danielss24/TFG_EPS_DSS/Memoria/Latex/varios/estudioDron.tex

Se han realizado numerosas configuraciones para estabilizar tiempo de vuelo y carga máxima del dron, obteniendo el mejor resultado en la imagen de a continuación \ref{FIG:estudioDron}.
\begin{figure}[Estudio técnico de dron]{FIG:estudioDron}{En esta imagen se muestran los datos obtenidos mediante una herramienta de internet, eCalc \cite{DroneConfig}, para el estudio de componentes para dron.}
	\image{1\textwidth}{}{estudioDron}
\end{figure}
