danielss24/TFG_EPS_DSS/Memoria/Latex/inicio/agradecimientos.tex

En primer lugar me gustaría agradecer el esfuerzo y empeño que han demostrado todas las personas del departamento donde he hecho este TFG, empezando por mi tutor Stefan Palzer, por guiarme y ayudarme a realizar este trabajo, a Álvaro Ortiz por sus consejos de recién doctorado y su ingenio que ha arreglado algún que otro problemilla y, sobre todo, a Patricia González, mi compañera de ideas y sufrimiento durante todo este proceso de investigación y desarrollo de nuestro trabajo de final de grado. 

Por otro lado quiero agradecer el apoyo que he recibido de mi familia ya que, sin ellos no podría haber finalizado esta etapa de mi vida plasmada en este último proyecto de la carrera que he llevado a cabo.

En último lugar pero no menos importante quiero agradecer a mis amigos y compañeros a los que han terminado o aún siguen en la carrera, especial mención a la promoción de este año con los que he compartido tanto risas como lágrimas. 

Muchas gracias a todos.
