danielss24/TFG_EPS_DSS/Memoria/Latex/varios/codigoPlotWind0.tex

\PythonCode[COD:CODIGOPLOTSCATTER]{Código de scatterFit}{Código de gráfica para imagen \ref{FIG:scatterFit}}{plotWind.py}{245}{281}{1}
