danielss24/TFG_EPS_DSS/Memoria/Latex/varios/codigoPlotWind1.tex

\PythonCode[COD:CODIGOHEATMAP]{Código de mapa de calor - parte 1}{Código de gráfica para imagen \ref{FIG:MAPACALOR}(a)}{plotWind.py}{283}{320}{1}

\PythonCode[COD:CODIGOHEATMAP2]{Código de mapa de calor - parte 2}{Código de gráfica para imagen \ref{FIG:MAPACALOR}(a)}{plotWind.py}{321}{328}{39}
