danielss24/TFG_EPS_DSS/Memoria/Latex/varios/codigoPlotWind2.tex

Para la ilustración de un mapa 2D con 4 vectores se ha tenido que realizar una conversión de un conjunto de puntos en un vector con dos direcciones.

\PythonCode[COD:CODIGOGRAFICA2D]{Código de gráfica 2D - parte 1}{Código de gráfica para imagen \ref{FIG:PLANOSMEDIDAS}(a) y \ref{FIG:PLANOSMEDIDAS}(b)}{plotWind.py}{330}{360}{1}

\PythonCode[COD:CODIGOGRAFICA2D2]{Código de gráfica 2D - parte 2}{Código de gráfica para imagen \ref{FIG:PLANOSMEDIDAS}(a) y \ref{FIG:PLANOSMEDIDAS}(b)}{plotWind.py}{361}{381}{61}
