danielss24/TFG_EPS_DSS/Memoria/Latex/varios/codigoPlotWind3.tex

La ilustración de los datos en 3D ha tenido que llevar a cabo una conversión de un conjunto de puntos variables en un vector, conformando de esta forma un mapa 3D de 8 vectores.

\PythonCode[COD:CODIGOGRAFICA3D]{Código de gráfica 3D - parte 1}{Código de gráfica para imagen \ref{FIG:mapa3d}}{plotWind.py}{383}{410}{1}

\PythonCode[COD:CODIGOGRAFICA3DPart2]{Código de gráfica 3D - parte 2}{Código de gráfica para imagen \ref{FIG:mapa3d}}{plotWind.py}{411}{461}{29}

\PythonCode[COD:CODIGOGRAFICA3DPart3]{Código de gráfica 3D - parte 3}{Código de gráfica para imagen \ref{FIG:mapa3d}}{plotWind.py}{462}{484}{79}
