danielss24/TFG_EPS_DSS/Documentacion/Dron/Old/HobbyKing ™ TORTAZO 300.docx

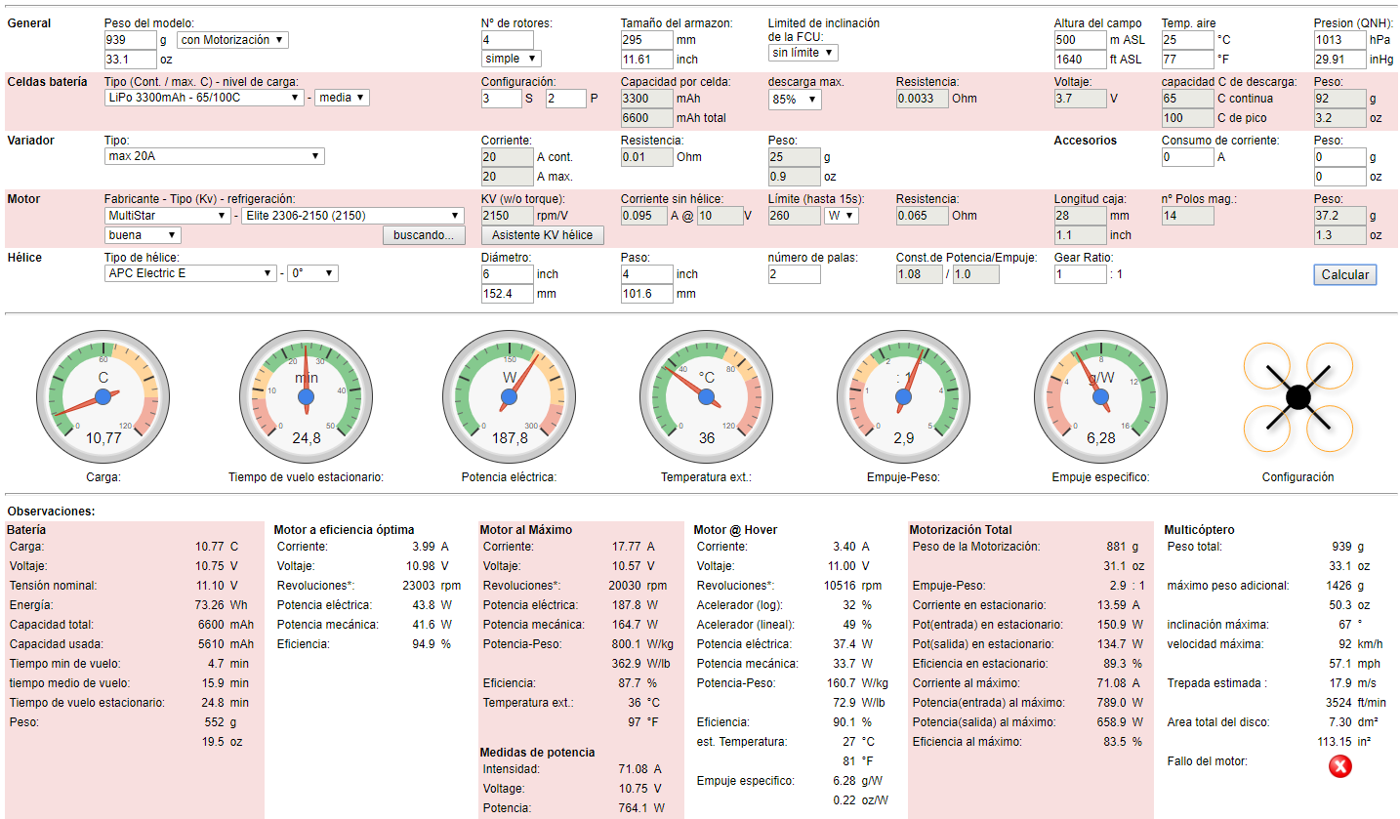
[picture p22: figure]
