danielss24/TFG_EPS_DSS/Memoria/Latex/img/3axisforces.png

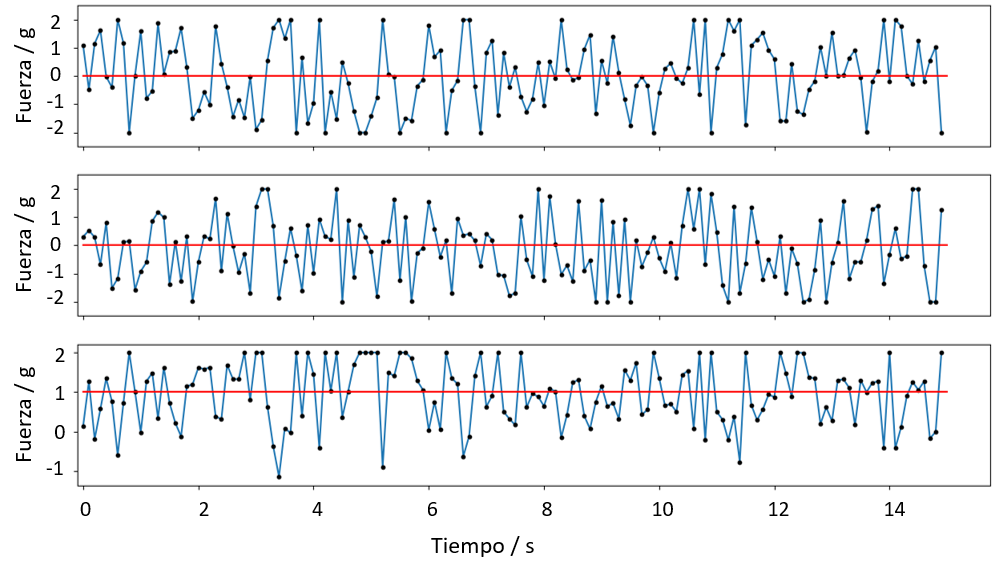
Memoria/Latex/img/3axisforces.png
