danielss24/TFG_EPS_DSS/Memoria/Latex/img/acoplamientosDron.png

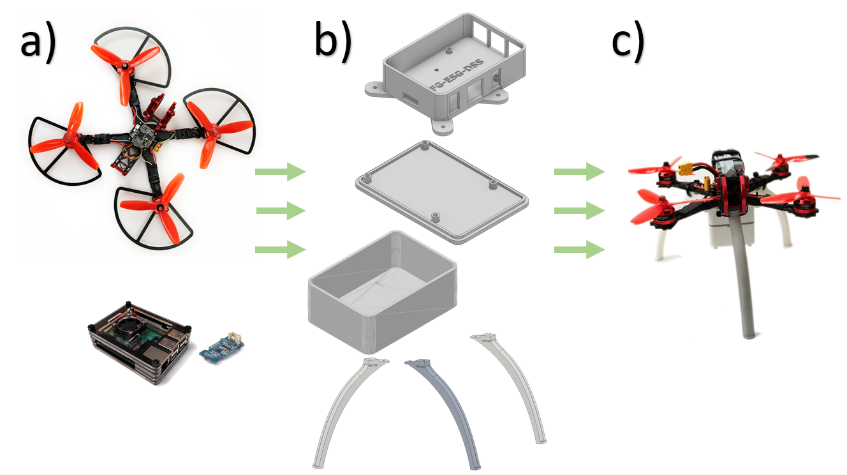
Memoria/Latex/img/acoplamientosDron.png
