danielss24/TFG_EPS_DSS/Memoria/Latex/img/bateriaDron.PNG

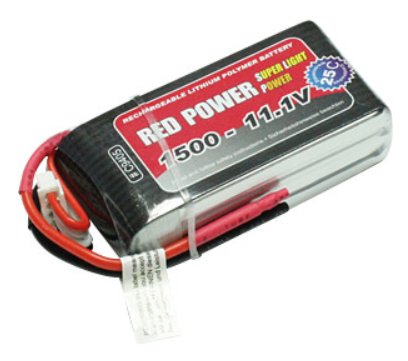
Memoria/Latex/img/bateriaDron.PNG
