danielss24/TFG_EPS_DSS/Memoria/Latex/img/chasis2Dron.PNG

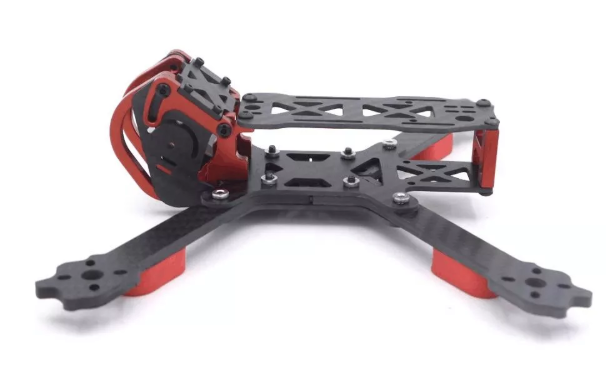
Memoria/Latex/img/chasis2Dron.PNG
