danielss24/TFG_EPS_DSS/Memoria/Latex/img/chasisDron.PNG

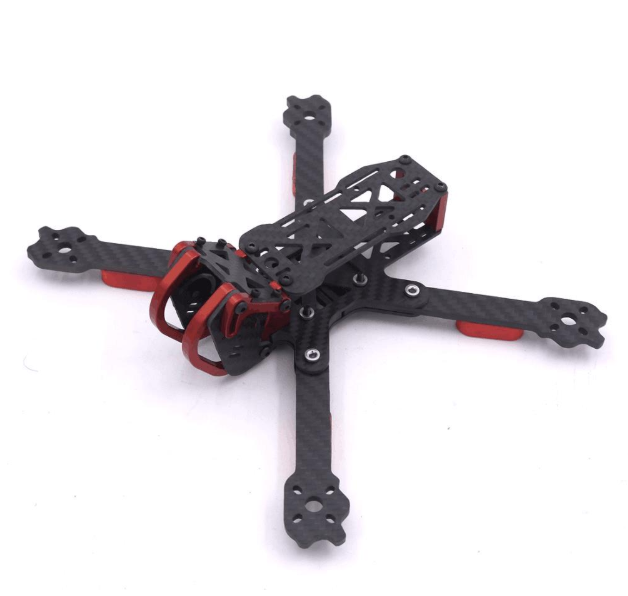
Memoria/Latex/img/chasisDron.PNG
