danielss24/TFG_EPS_DSS/Memoria/Latex/img/ChasisRaspberryDron.PNG

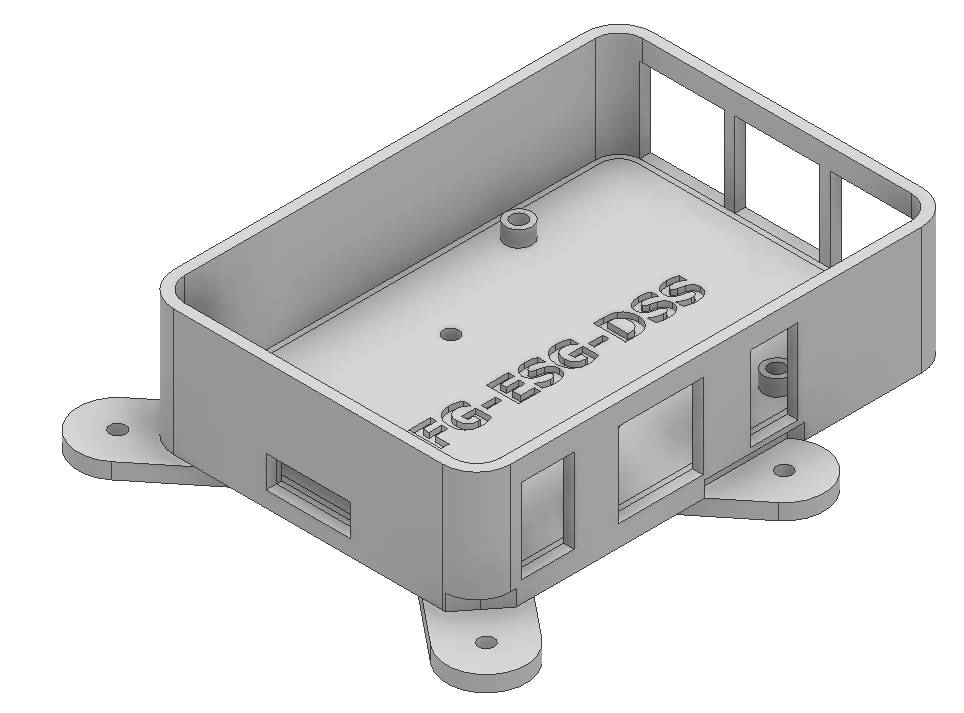
Memoria/Latex/img/ChasisRaspberryDron.PNG
