danielss24/TFG_EPS_DSS/Memoria/Latex/img/controladoraDron.PNG

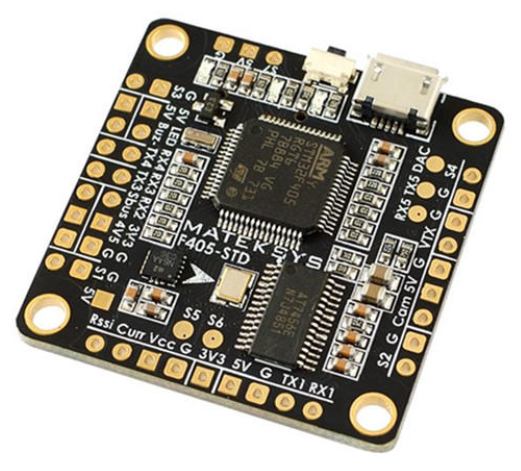
Memoria/Latex/img/controladoraDron.PNG
