danielss24/TFG_EPS_DSS/Memoria/Latex/img/diagramaPlacaControladora2.png

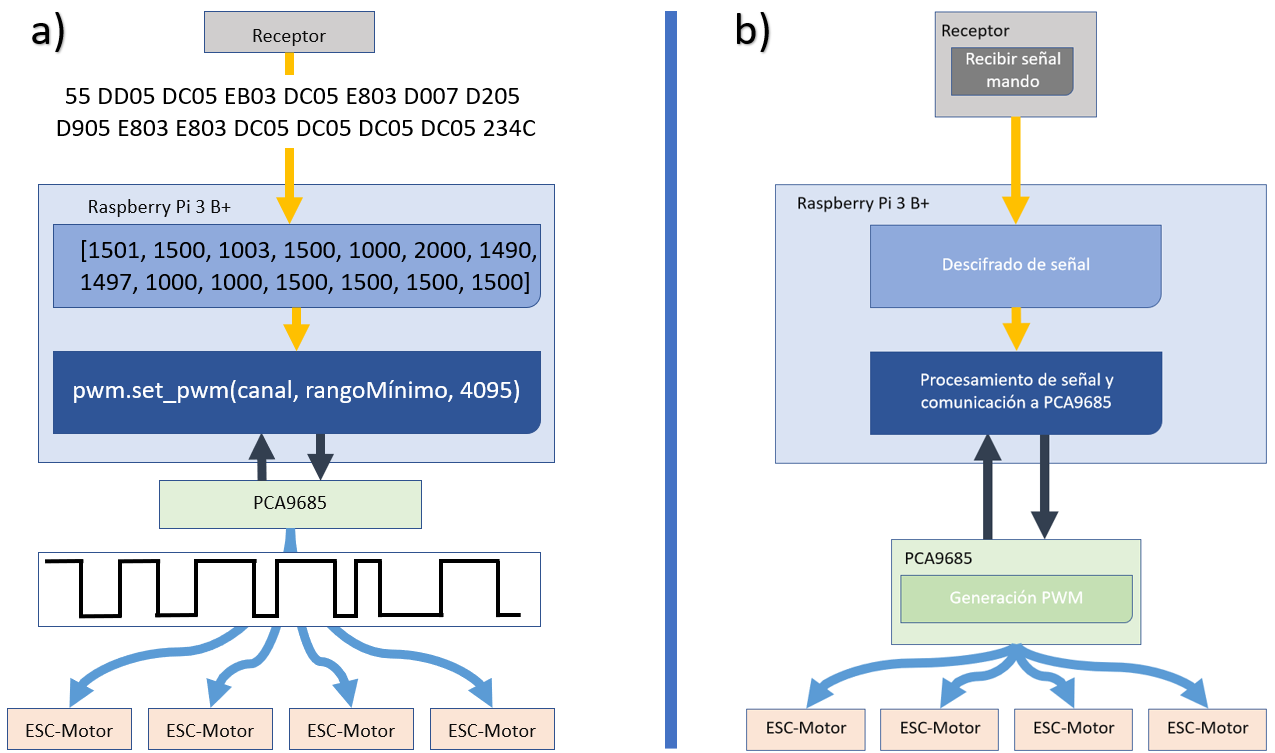
Memoria/Latex/img/diagramaPlacaControladora2.png
