danielss24/TFG_EPS_DSS/Memoria/Latex/img/diagramaPlacaControladora.png

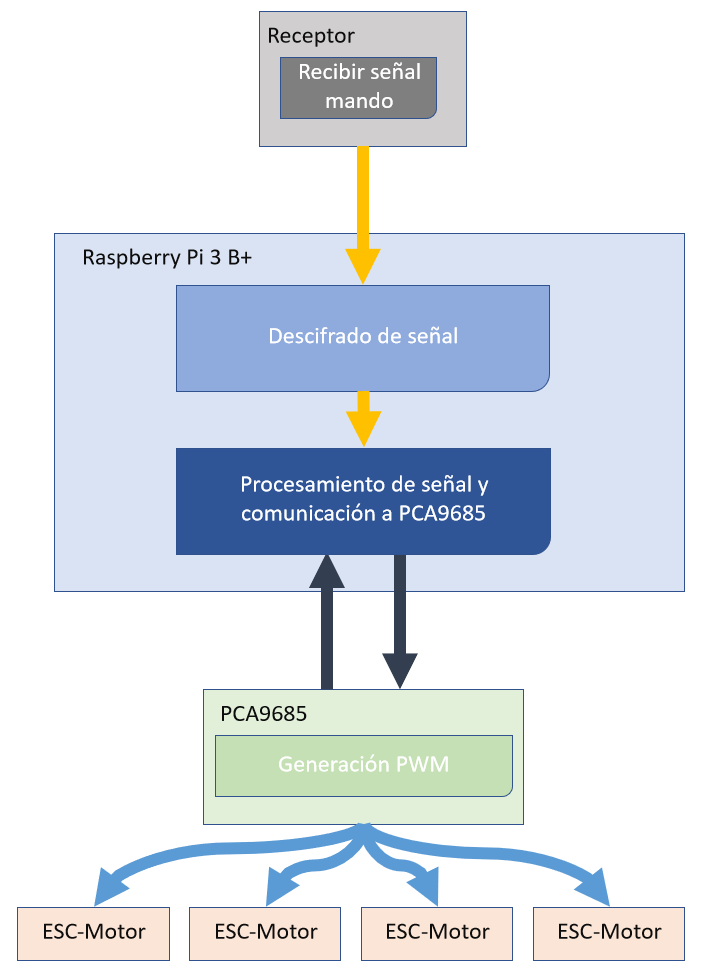
Memoria/Latex/img/diagramaPlacaControladora.png
