danielss24/TFG_EPS_DSS/Memoria/Latex/img/dronCompleto2.jpg

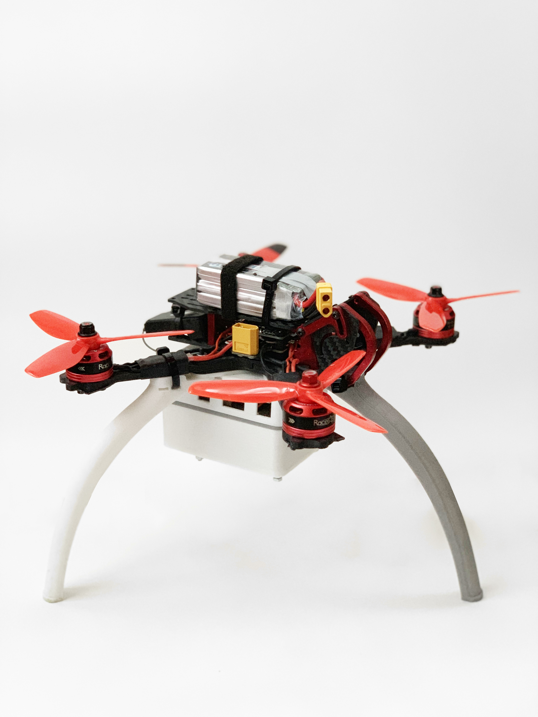
Memoria/Latex/img/dronCompleto2.jpg
