danielss24/TFG_EPS_DSS/Memoria/Latex/img/dronCompleto.jpg

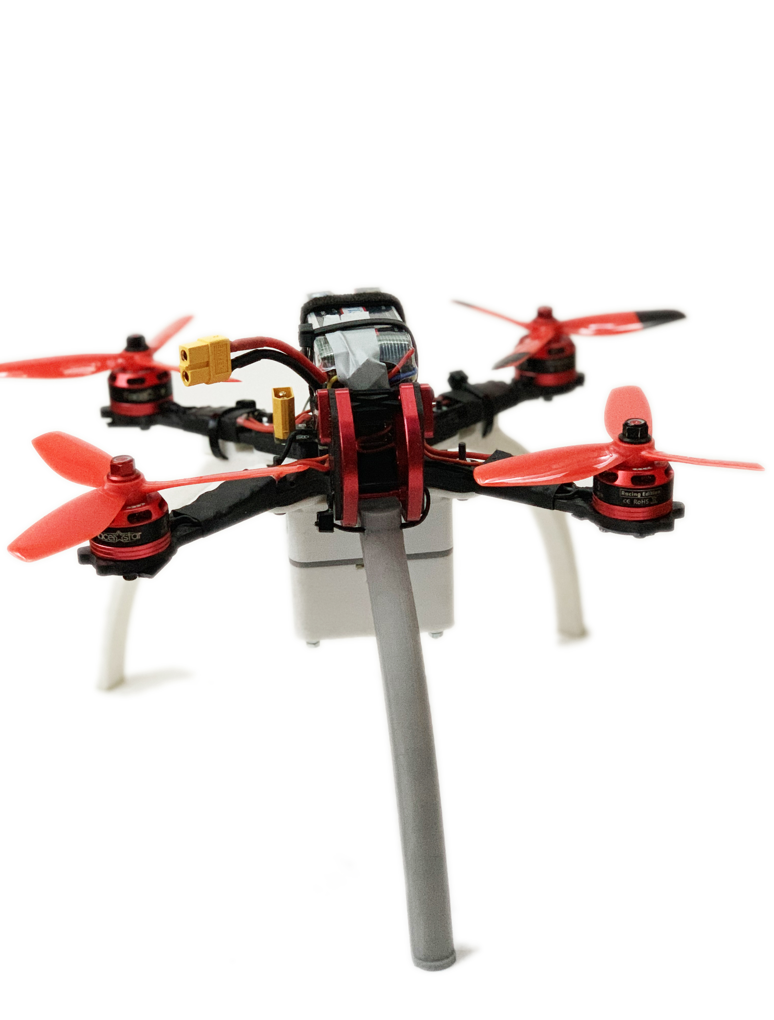
Memoria/Latex/img/dronCompleto.jpg
