danielss24/TFG_EPS_DSS/Memoria/Latex/img/dronVirgen2.jpg

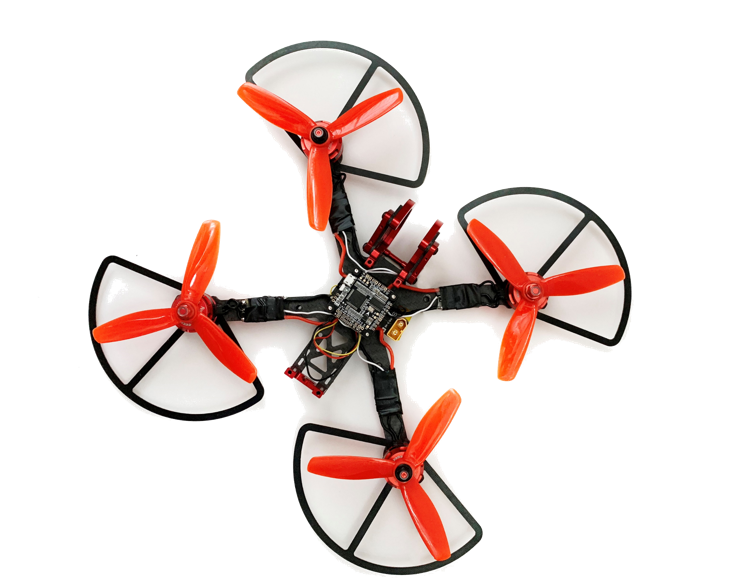
Memoria/Latex/img/dronVirgen2.jpg
