danielss24/TFG_EPS_DSS/Memoria/Latex/img/dronVirgen.jpg

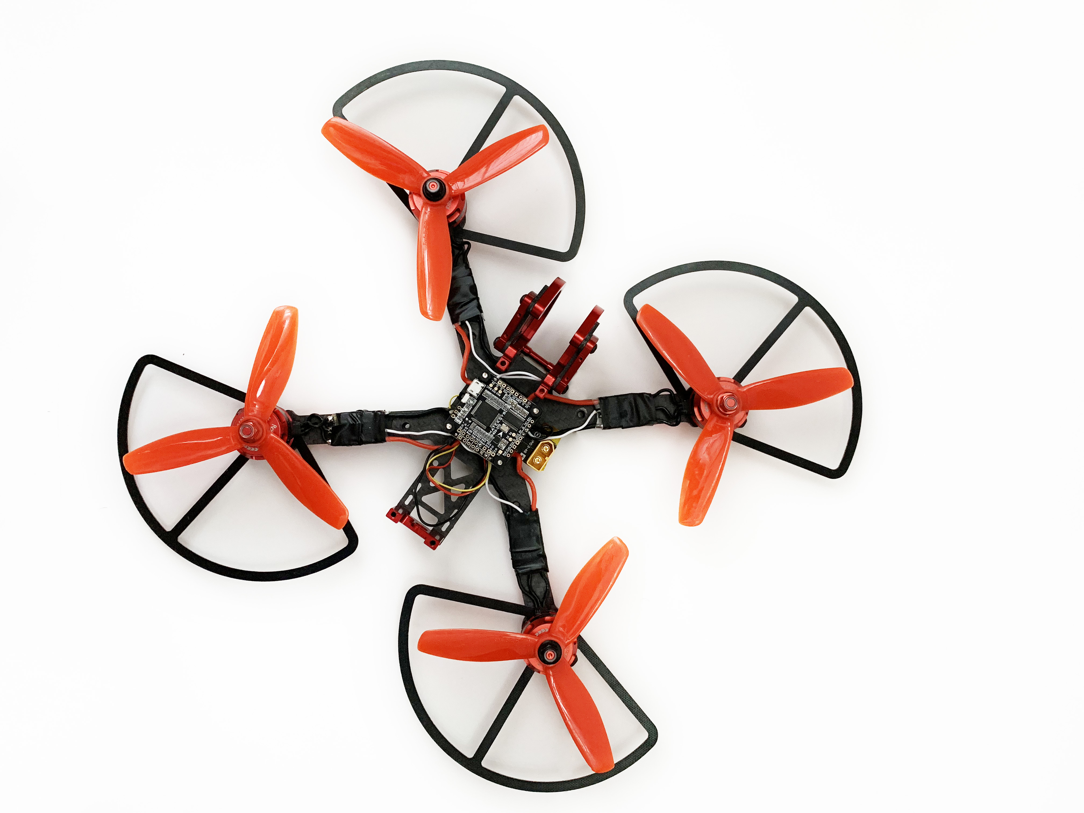
Memoria/Latex/img/dronVirgen.jpg
