danielss24/TFG_EPS_DSS/Memoria/Latex/img/dronVirgenPartes2.png

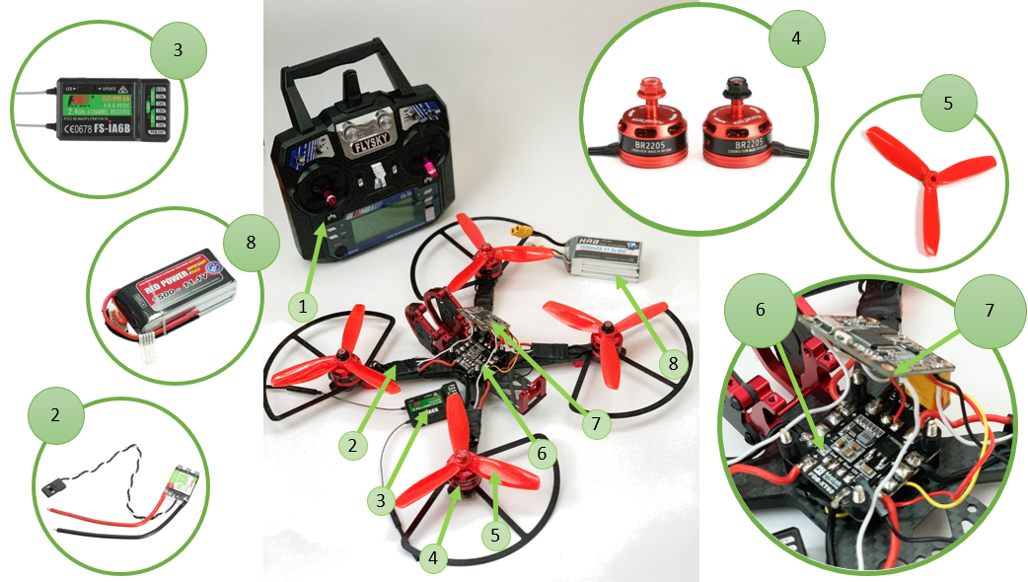
Memoria/Latex/img/dronVirgenPartes2.png
