danielss24/TFG_EPS_DSS/Memoria/Latex/img/dronVirgenPartes3.png

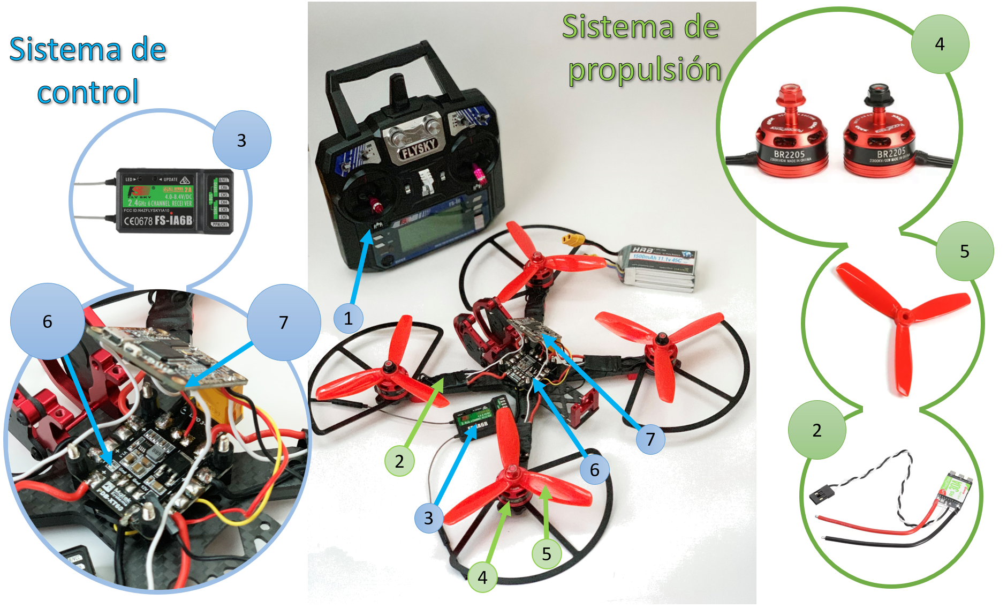
Memoria/Latex/img/dronVirgenPartes3.png
