danielss24/TFG_EPS_DSS/Memoria/Latex/img/dronVirgenPartes.png

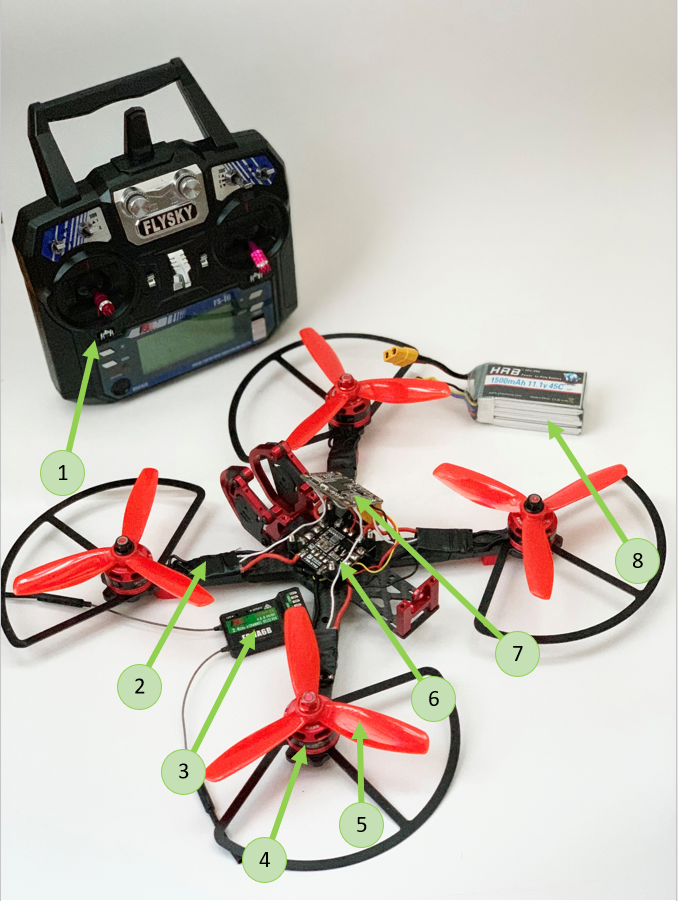
Memoria/Latex/img/dronVirgenPartes.png
