danielss24/TFG_EPS_DSS/Memoria/Latex/img/escDron.PNG

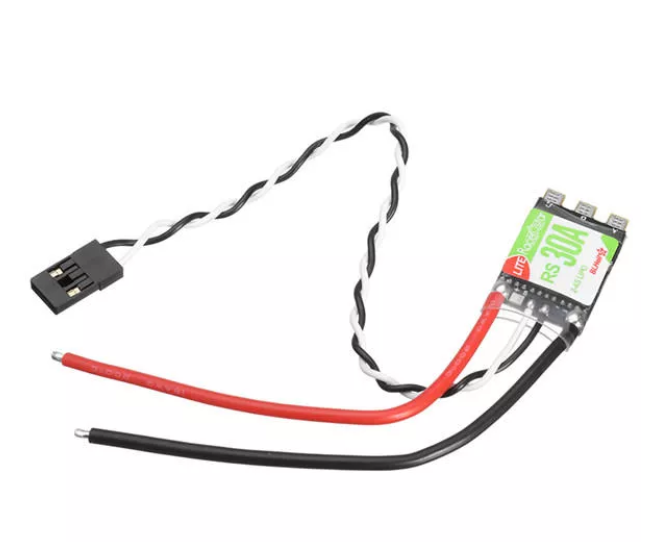
Memoria/Latex/img/escDron.PNG
