danielss24/TFG_EPS_DSS/Memoria/Latex/img/estructuraPrograma.png

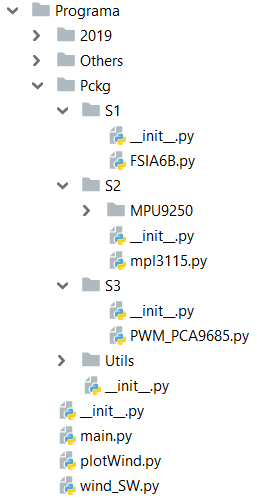
Memoria/Latex/img/estructuraPrograma.png
