danielss24/TFG_EPS_DSS/Memoria/Latex/img/gimansio0.jpg

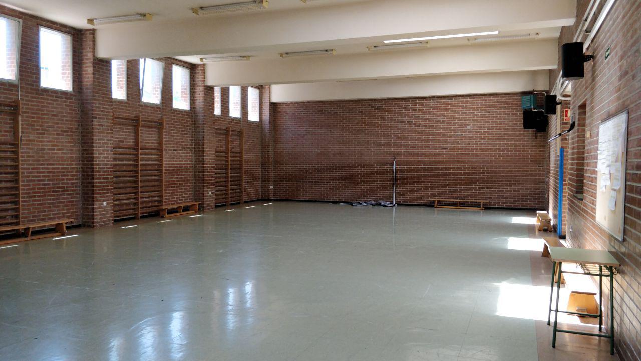
Memoria/Latex/img/gimansio0.jpg
