danielss24/TFG_EPS_DSS/Memoria/Latex/img/gimansio1.jpg

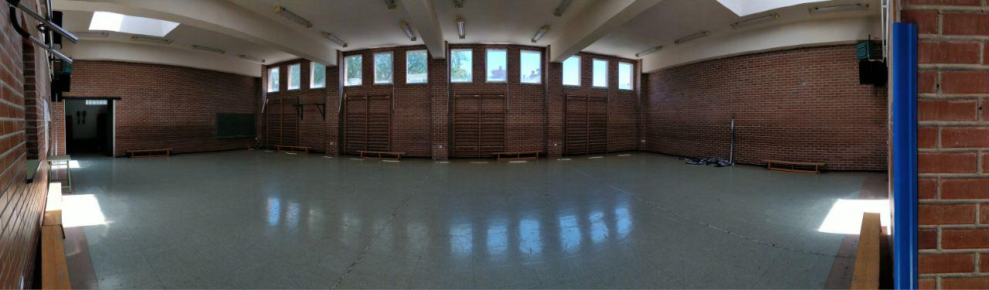
Memoria/Latex/img/gimansio1.jpg
