danielss24/TFG_EPS_DSS/Memoria/Latex/img/gimnasioPanoramicaPtsToma.png

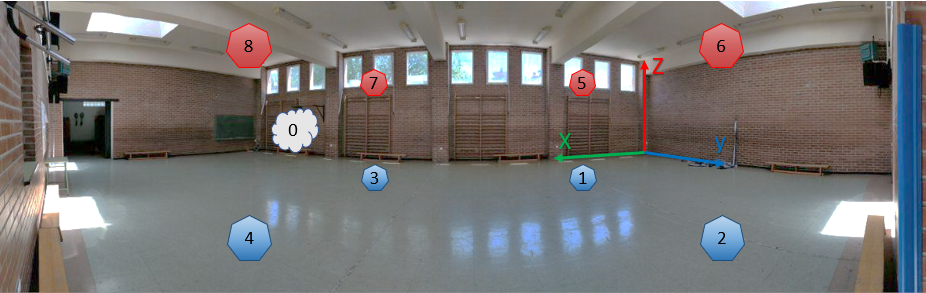
Memoria/Latex/img/gimnasioPanoramicaPtsToma.png
