danielss24/TFG_EPS_DSS/Memoria/Latex/img/gimnasioPanorámicaPtsToma.PNG

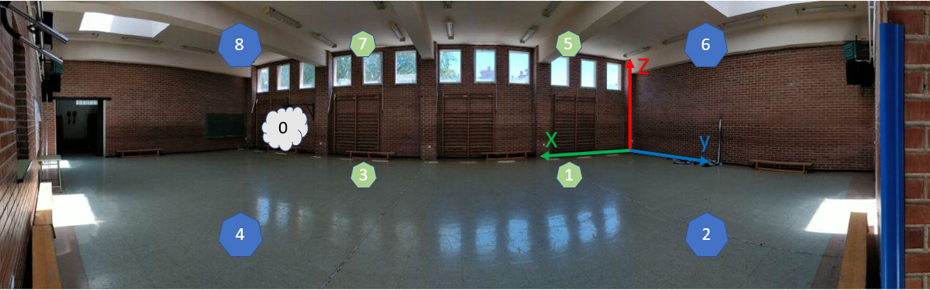
Memoria/Latex/img/gimnasioPanorámicaPtsToma.PNG
