danielss24/TFG_EPS_DSS/Memoria/Latex/img/graficasMapaCalor.png

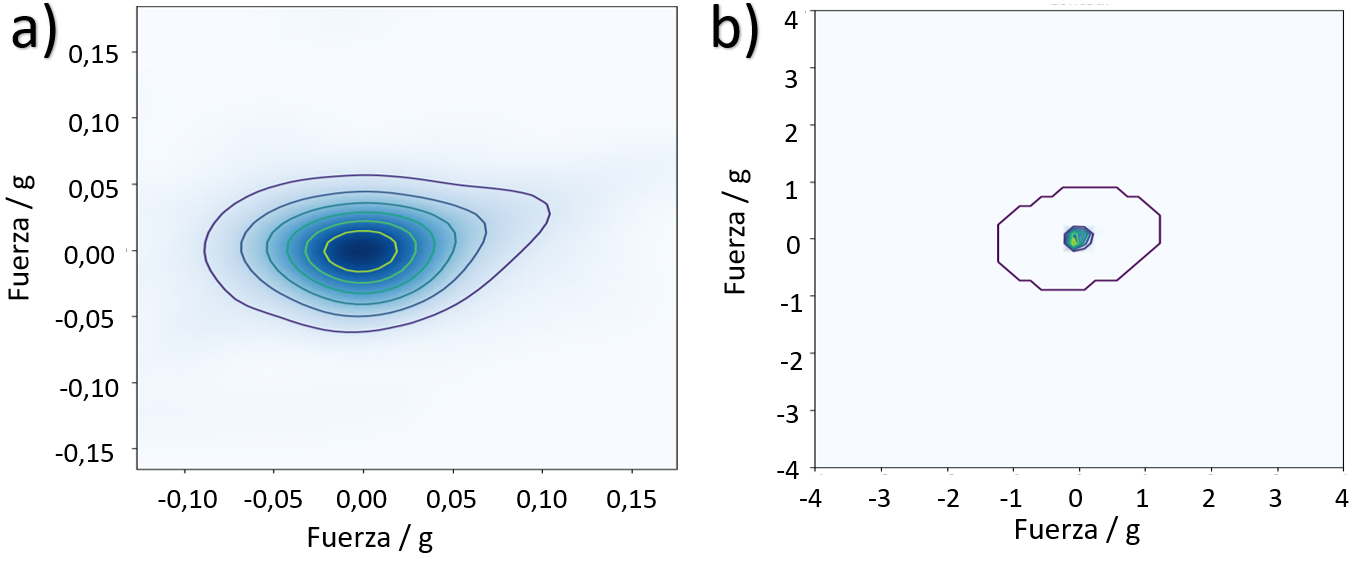
Memoria/Latex/img/graficasMapaCalor.png
