danielss24/TFG_EPS_DSS/Memoria/Latex/img/graficasplanoz0z1.png

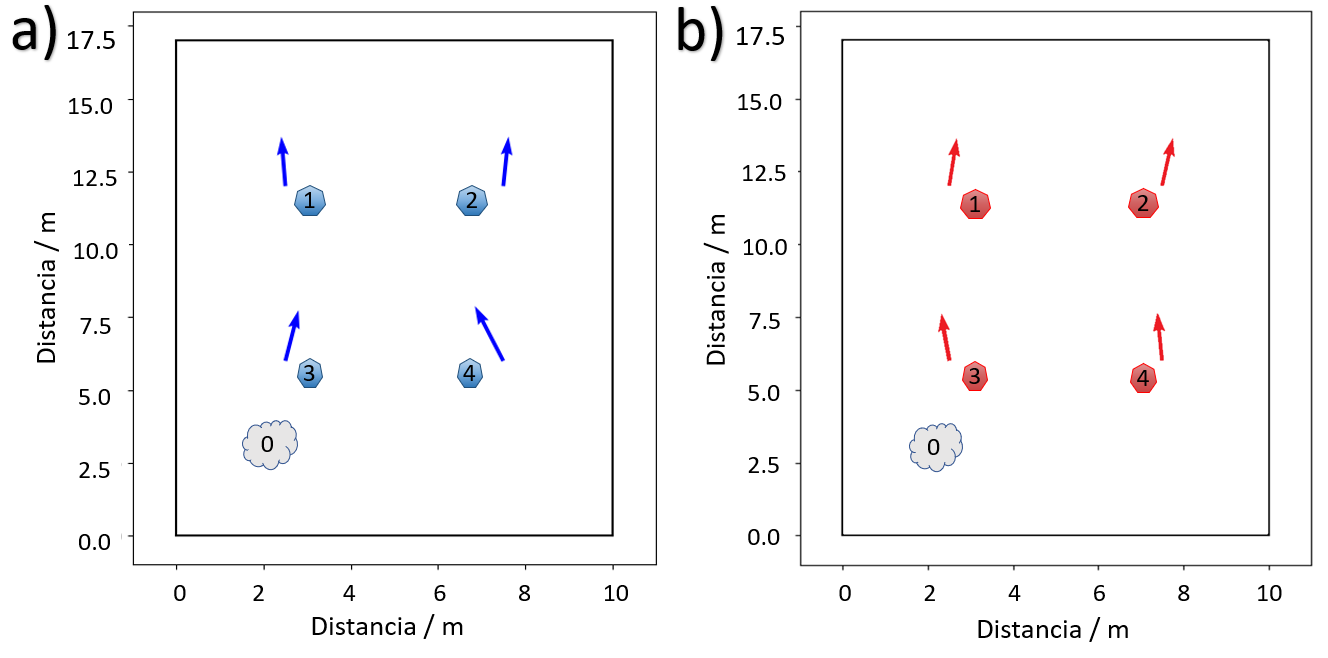
Memoria/Latex/img/graficasplanoz0z1.png
