danielss24/TFG_EPS_DSS/Memoria/Latex/img/heliceBullnose.PNG

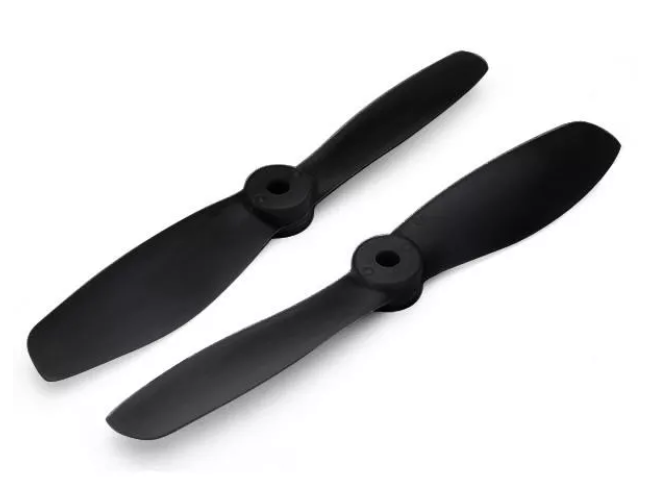
Memoria/Latex/img/heliceBullnose.PNG
