danielss24/TFG_EPS_DSS/Memoria/Latex/img/heliceHBullnose.jpg

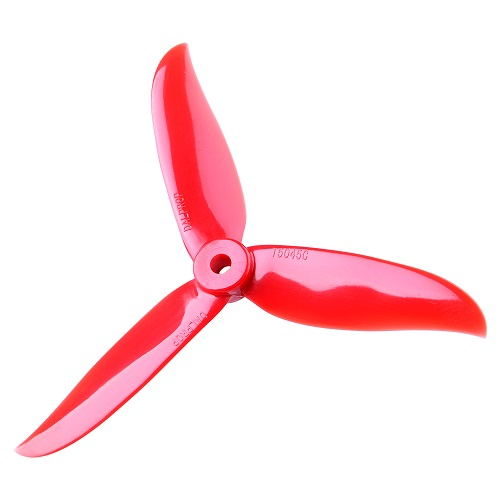
Memoria/Latex/img/heliceHBullnose.jpg
