danielss24/TFG_EPS_DSS/Memoria/Latex/img/helicePunta.jpg

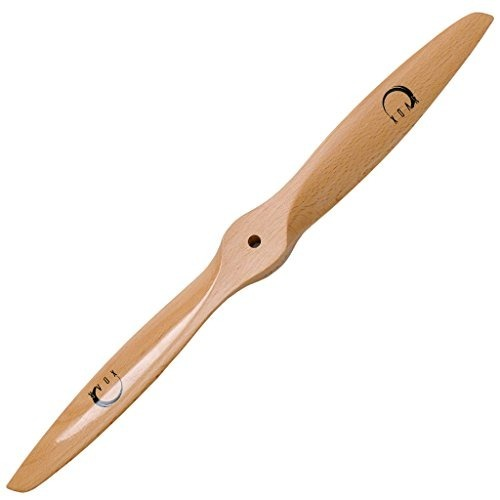
Memoria/Latex/img/helicePunta.jpg
