danielss24/TFG_EPS_DSS/Memoria/Latex/img/helicesDron.PNG

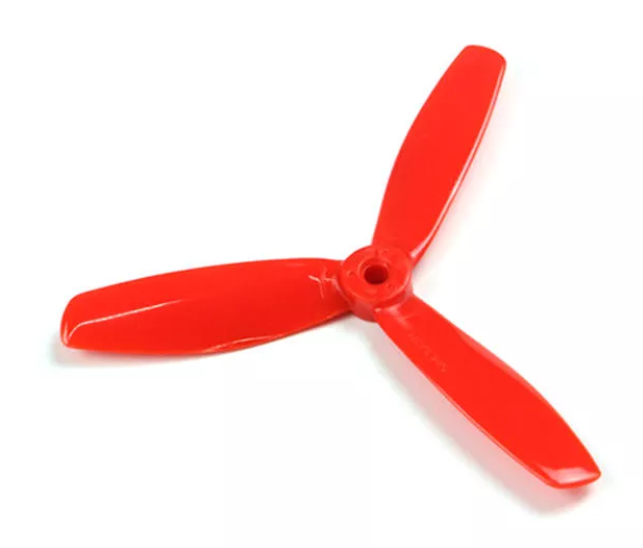
Memoria/Latex/img/helicesDron.PNG
