danielss24/TFG_EPS_DSS/Memoria/Latex/img/IMUAXES.png

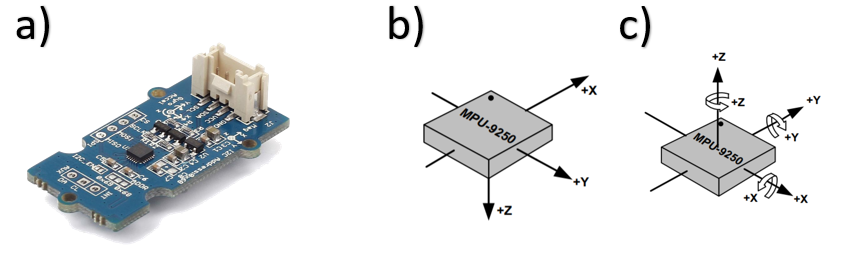
Memoria/Latex/img/IMUAXES.png
