danielss24/TFG_EPS_DSS/Memoria/Latex/img/introImg.png

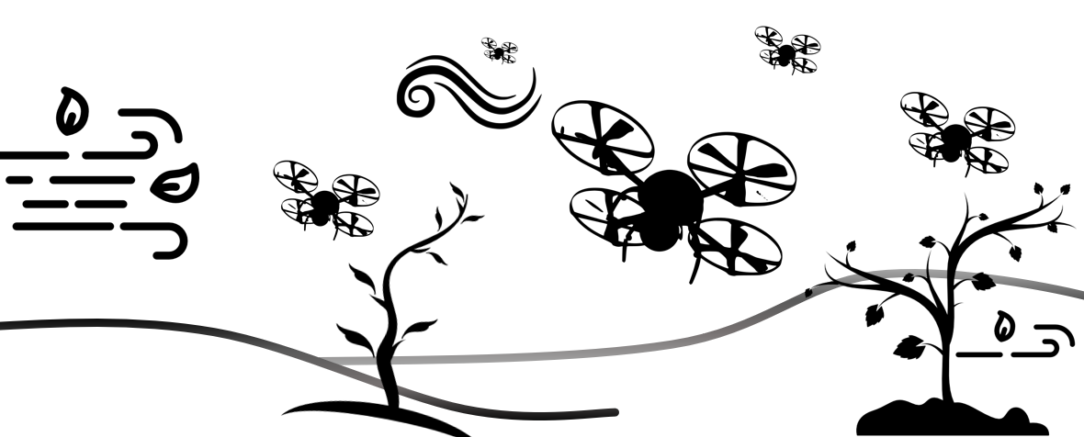
Memoria/Latex/img/introImg.png
