danielss24/TFG_EPS_DSS/Memoria/Latex/img/mandoDron.PNG

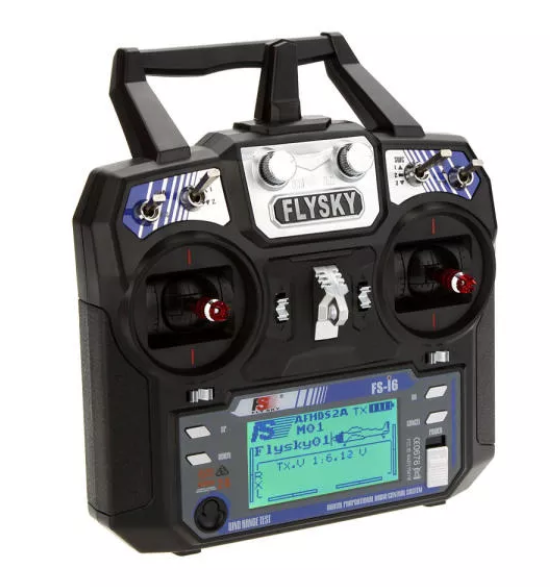
Memoria/Latex/img/mandoDron.PNG
