danielss24/TFG_EPS_DSS/Memoria/Latex/img/mapa3d.png

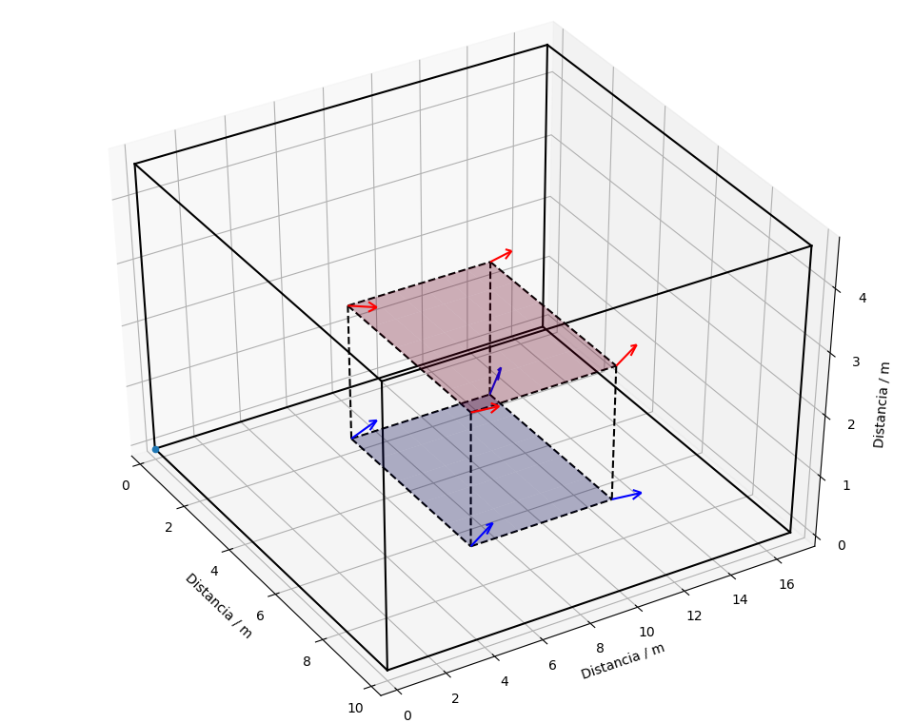
Memoria/Latex/img/mapa3d.png
