danielss24/TFG_EPS_DSS/Memoria/Latex/img/mapaCalor2.png

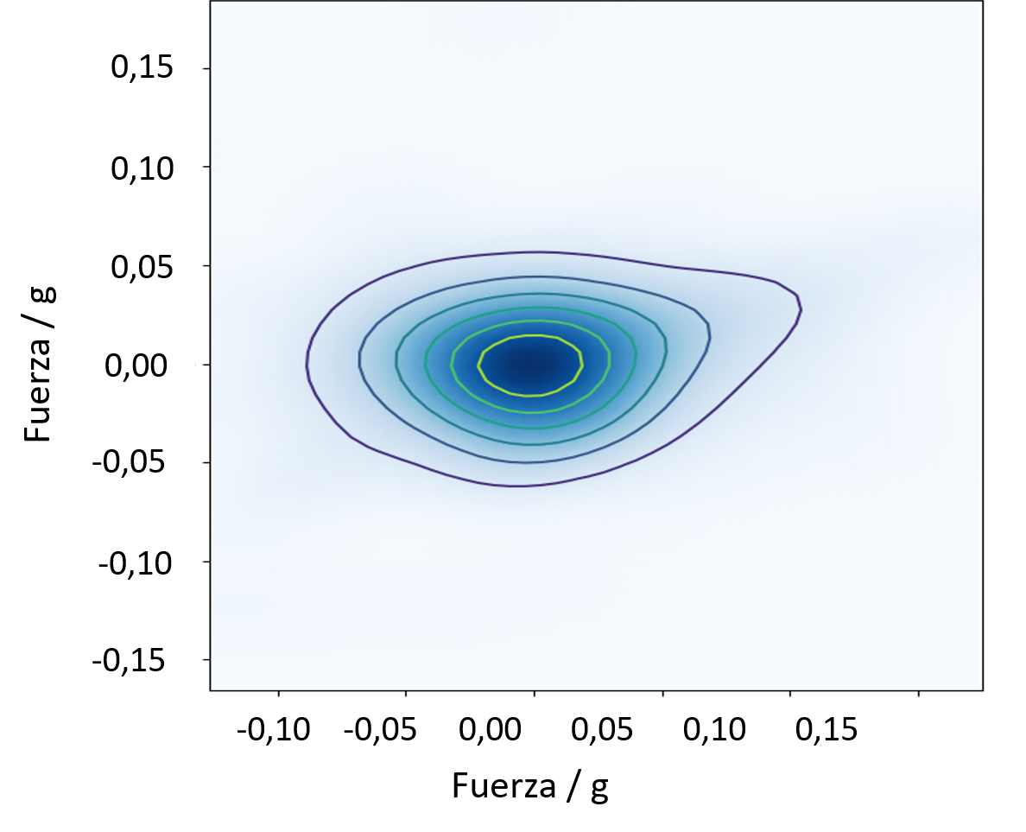
Memoria/Latex/img/mapaCalor2.png
