danielss24/TFG_EPS_DSS/Memoria/Latex/img/mapaCalor.png

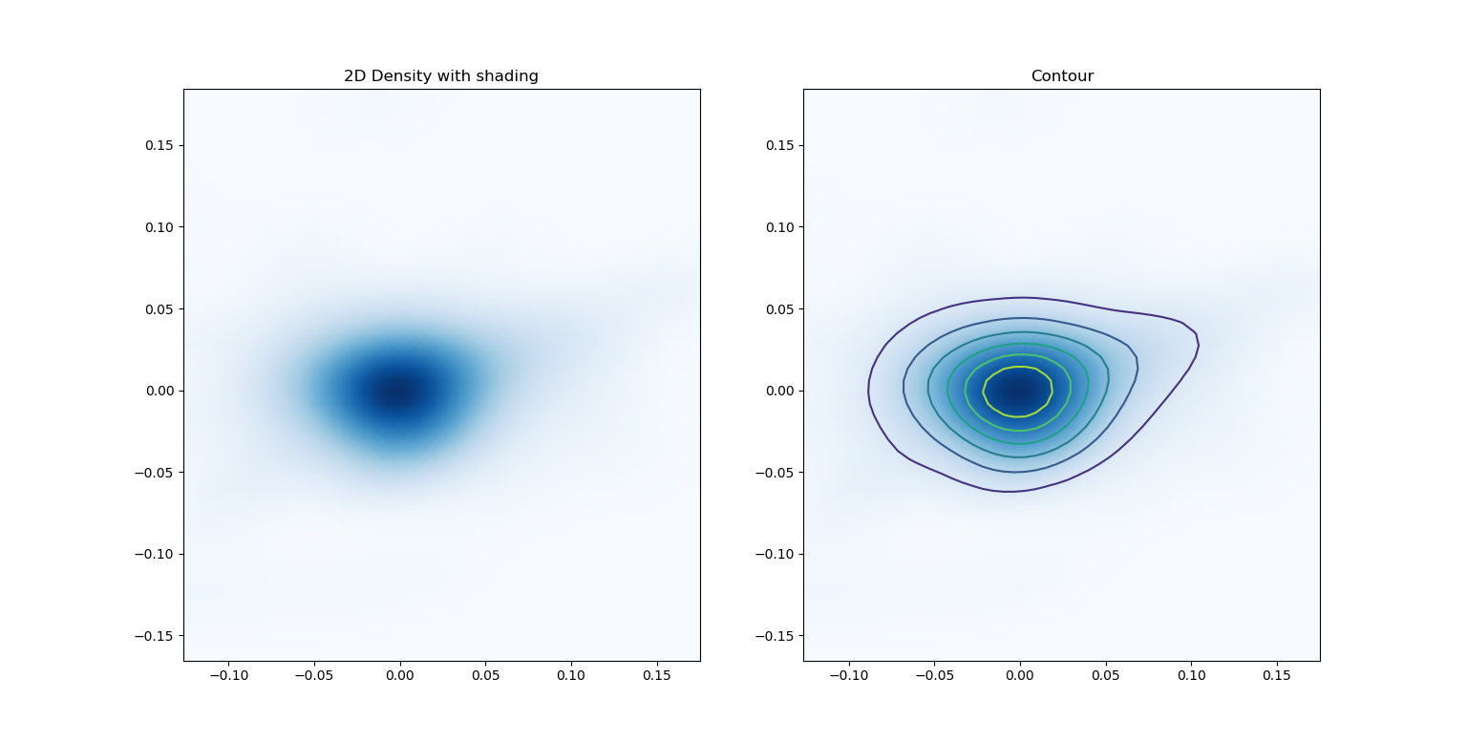
Memoria/Latex/img/mapaCalor.png
