danielss24/TFG_EPS_DSS/Memoria/Latex/img/mapaCalorSZ2.png

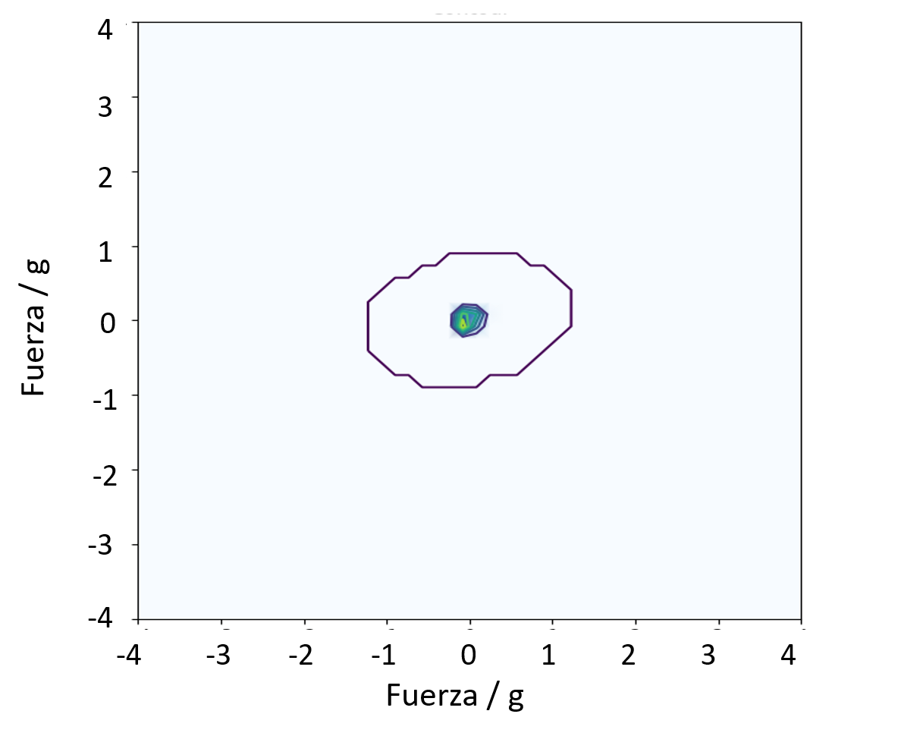
Memoria/Latex/img/mapaCalorSZ2.png
