danielss24/TFG_EPS_DSS/Memoria/Latex/img/mapaCalorSZ.png

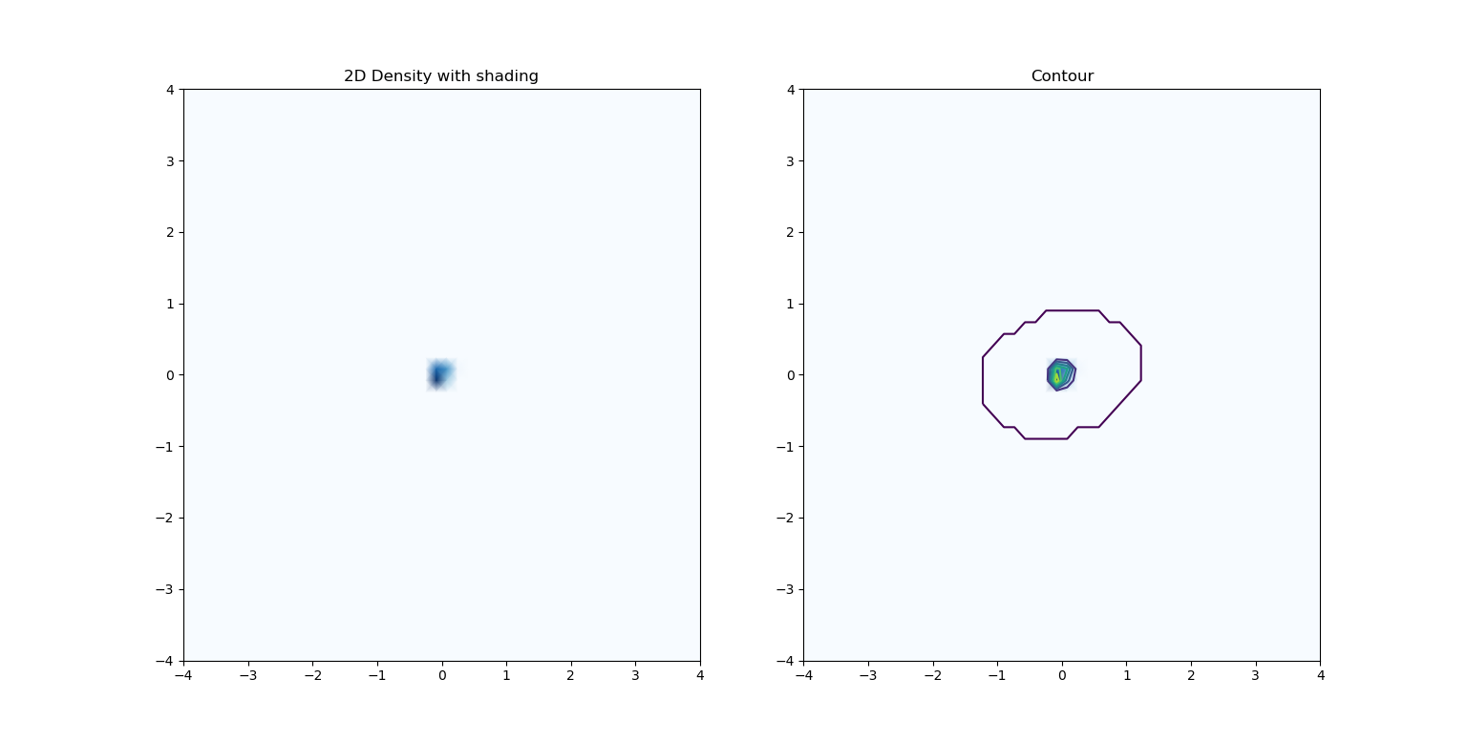
Memoria/Latex/img/mapaCalorSZ.png
