danielss24/TFG_EPS_DSS/Memoria/Latex/img/motoresDron.PNG

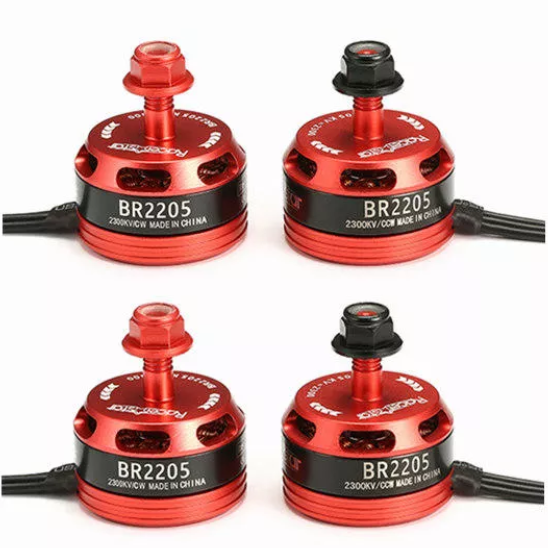
Memoria/Latex/img/motoresDron.PNG
