danielss24/TFG_EPS_DSS/Memoria/Latex/img/mpu9250AXES.png

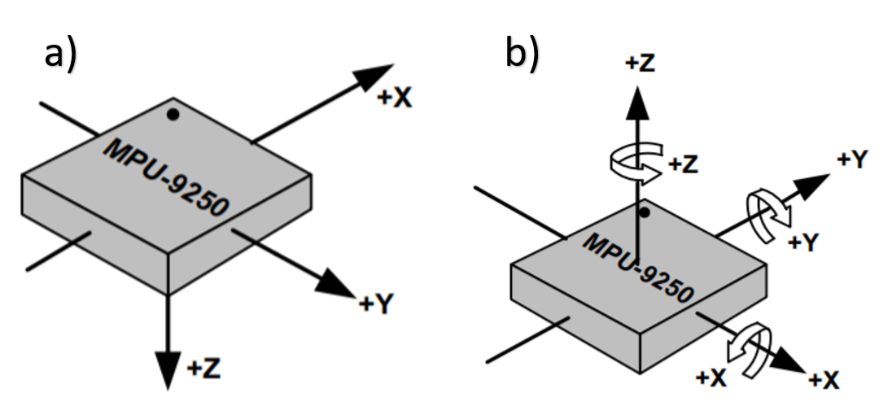
Memoria/Latex/img/mpu9250AXES.png
