danielss24/TFG_EPS_DSS/Memoria/Latex/img/PataDron.PNG

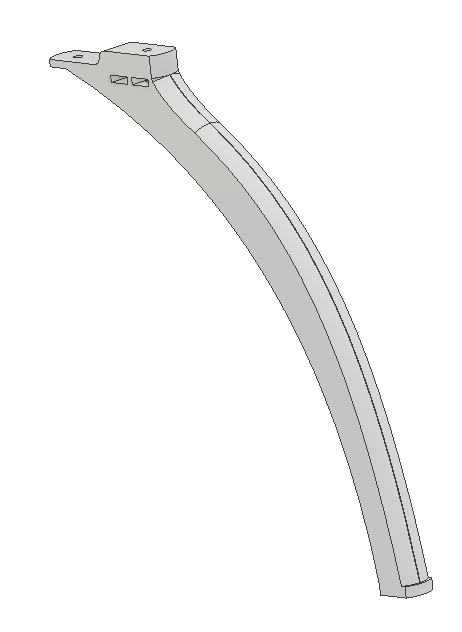
Memoria/Latex/img/PataDron.PNG
