danielss24/TFG_EPS_DSS/Memoria/Latex/img/pdbDron.PNG

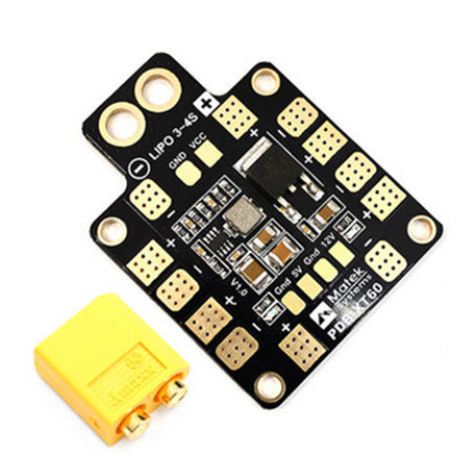
Memoria/Latex/img/pdbDron.PNG
