danielss24/TFG_EPS_DSS/Memoria/Latex/img/planoGimnasio.png

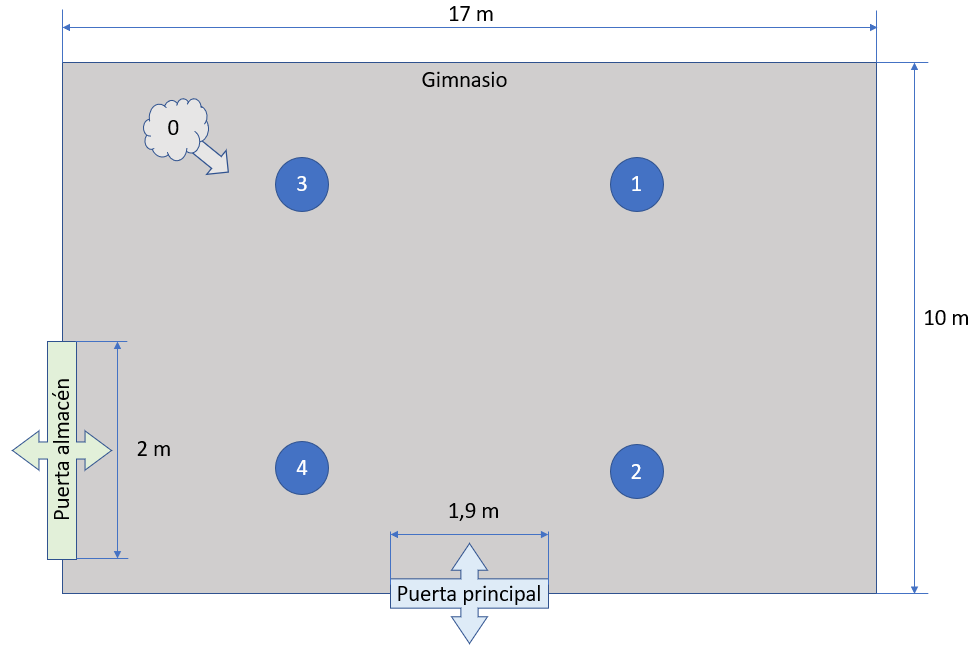
Memoria/Latex/img/planoGimnasio.png
