danielss24/TFG_EPS_DSS/Memoria/Latex/img/Plots/3axisforces.png

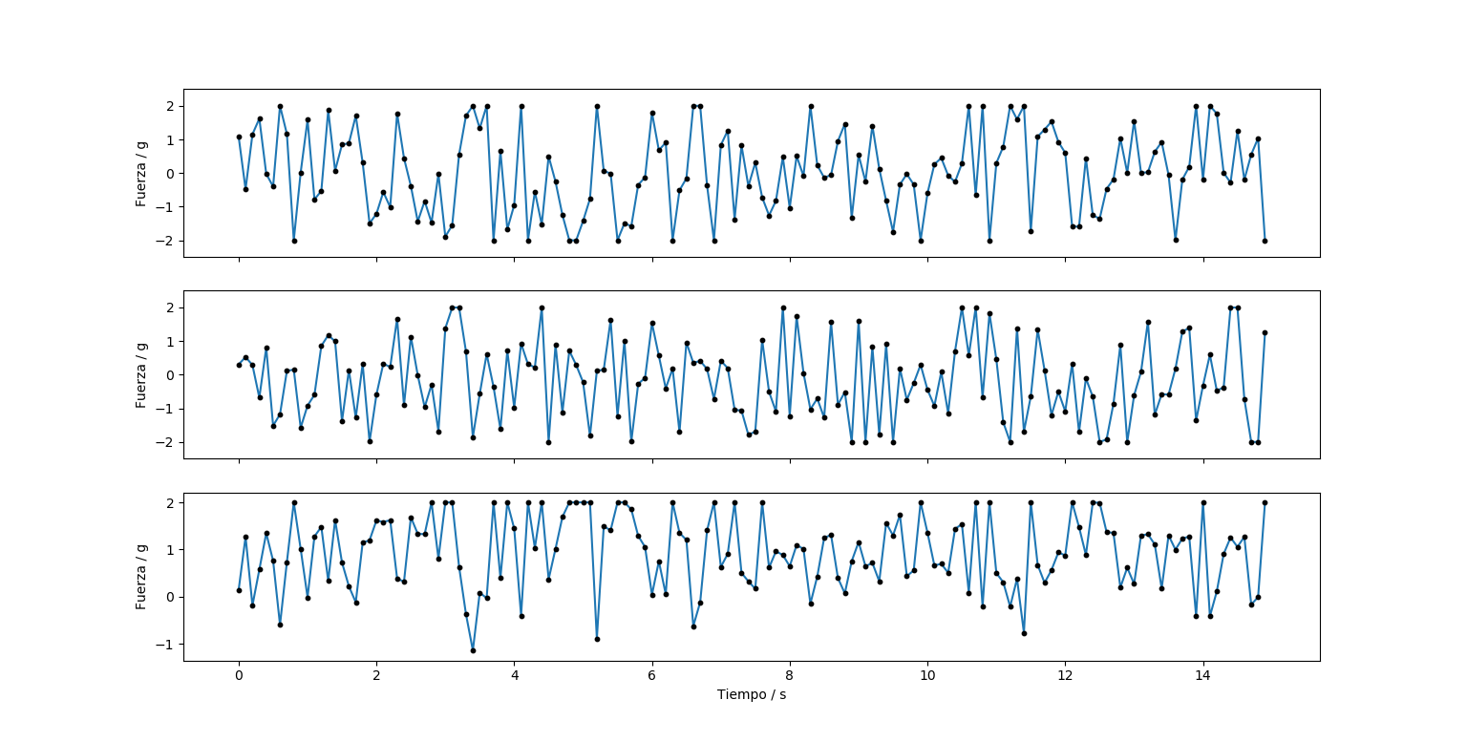
Memoria/Latex/img/Plots/3axisforces.png
