danielss24/TFG_EPS_DSS/Memoria/Latex/img/Plots/scatterFit.png

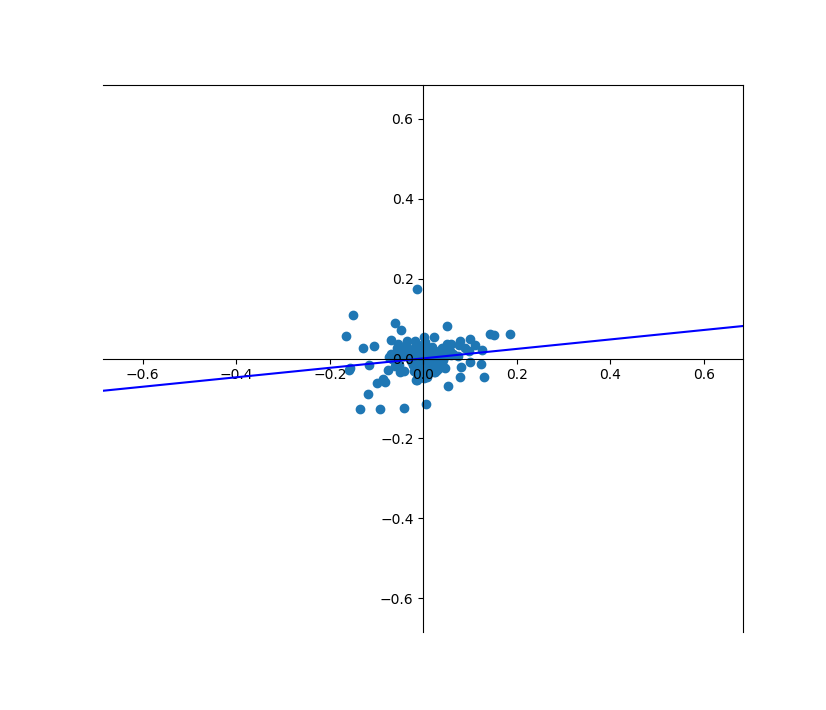
Memoria/Latex/img/Plots/scatterFit.png
