danielss24/TFG_EPS_DSS/Memoria/Latex/img/Plots/z0MapaViento.png

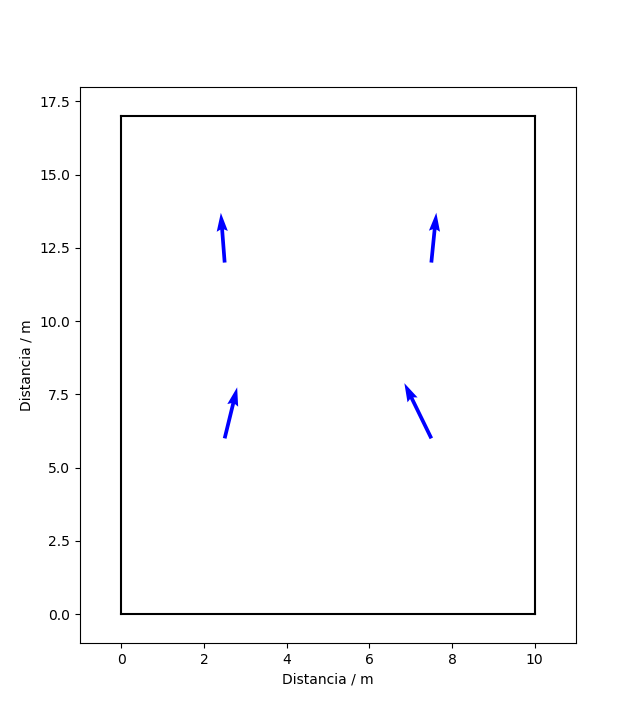
Memoria/Latex/img/Plots/z0MapaViento.png
