danielss24/TFG_EPS_DSS/Memoria/Latex/img/protectoresDron.PNG

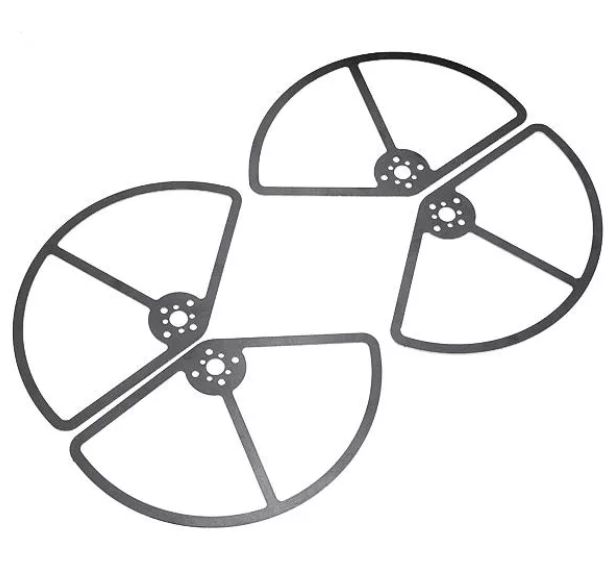
Memoria/Latex/img/protectoresDron.PNG
