danielss24/TFG_EPS_DSS/Memoria/Latex/img/RaspiSensor2.jpg

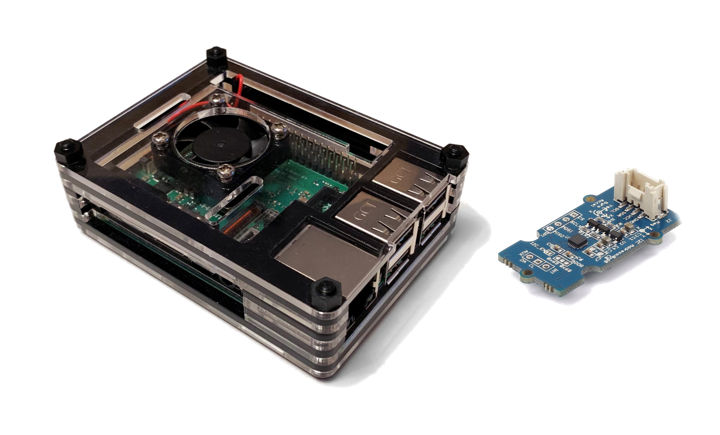
Memoria/Latex/img/RaspiSensor2.jpg
