danielss24/TFG_EPS_DSS/Memoria/Latex/img/RaspiSensor.jpg

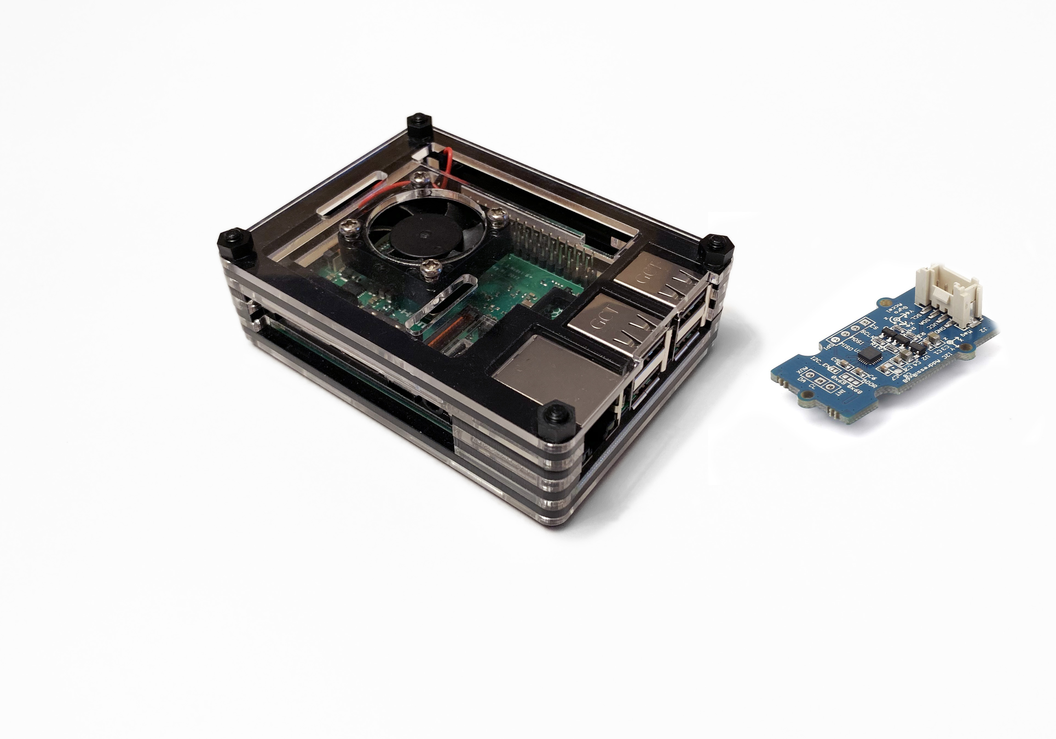
Memoria/Latex/img/RaspiSensor.jpg
