danielss24/TFG_EPS_DSS/Memoria/Latex/img/scatterFit.png

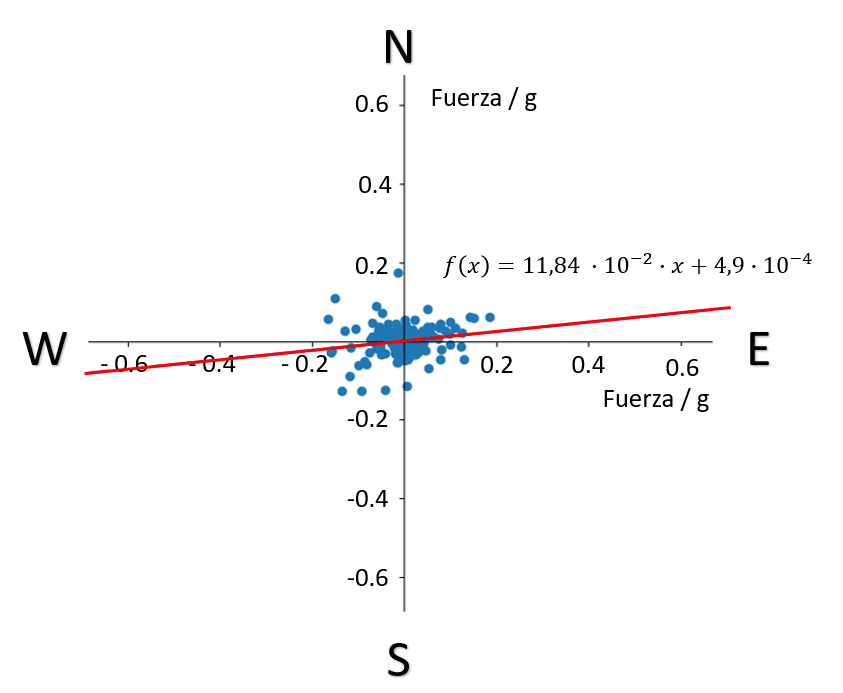
Memoria/Latex/img/scatterFit.png
