danielss24/TFG_EPS_DSS/Memoria/Latex/img/TapaChasisDron2.PNG

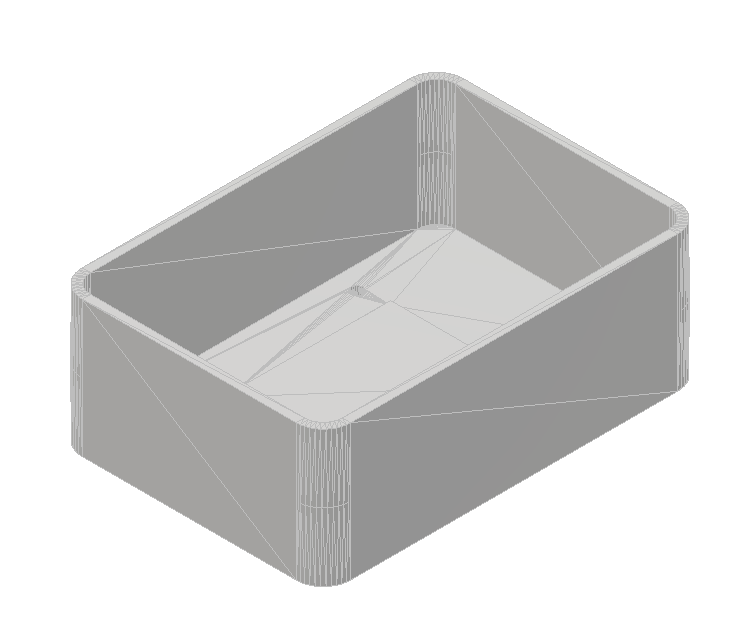
Memoria/Latex/img/TapaChasisDron2.PNG
