danielss24/TFG_EPS_DSS/Memoria/Latex/img/TapaChasisDron.PNG

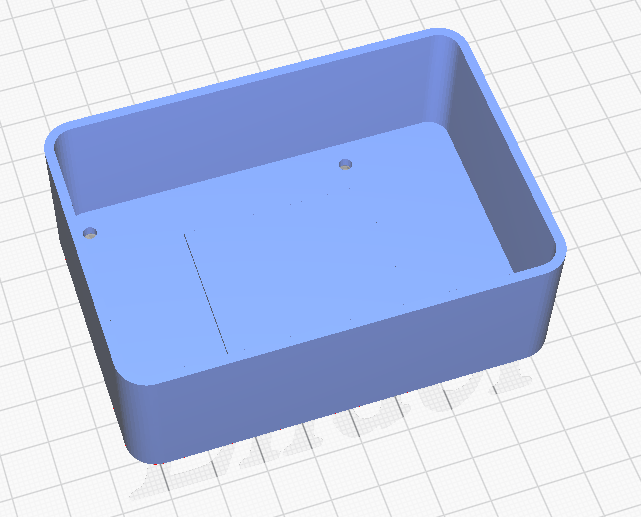
Memoria/Latex/img/TapaChasisDron.PNG
