danielss24/TFG_EPS_DSS/Memoria/Latex/img/TapaIntermediaDron.PNG

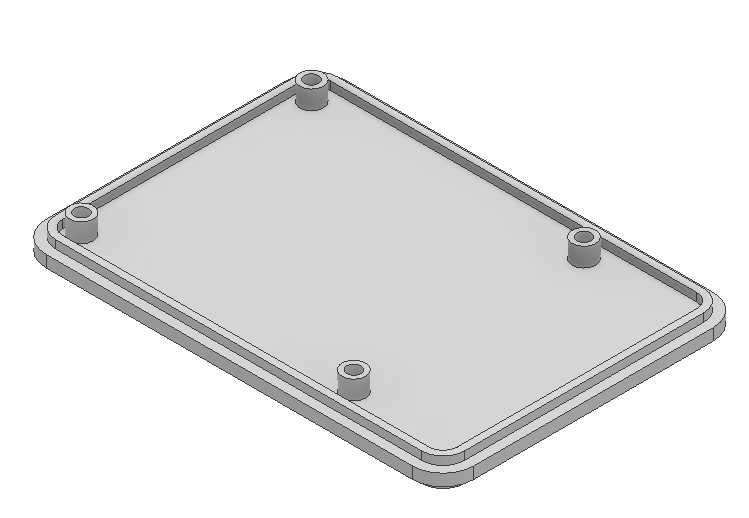
Memoria/Latex/img/TapaIntermediaDron.PNG
