danielss24/TFG_EPS_DSS/Memoria/Latex/img/tiposanemometros.png

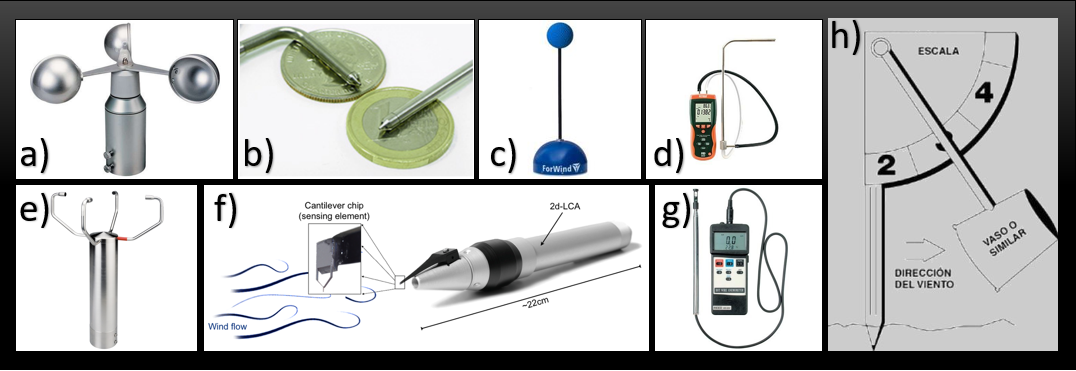
Memoria/Latex/img/tiposanemometros.png
