danielss24/TFG_EPS_DSS/Memoria/Latex/img/warningFoto.png

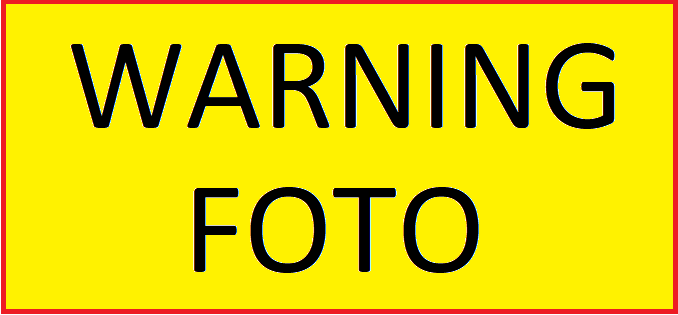
Memoria/Latex/img/warningFoto.png
