danielss24/TFG_EPS_DSS/Memoria/Latex/img/yawpitchrollplane.png

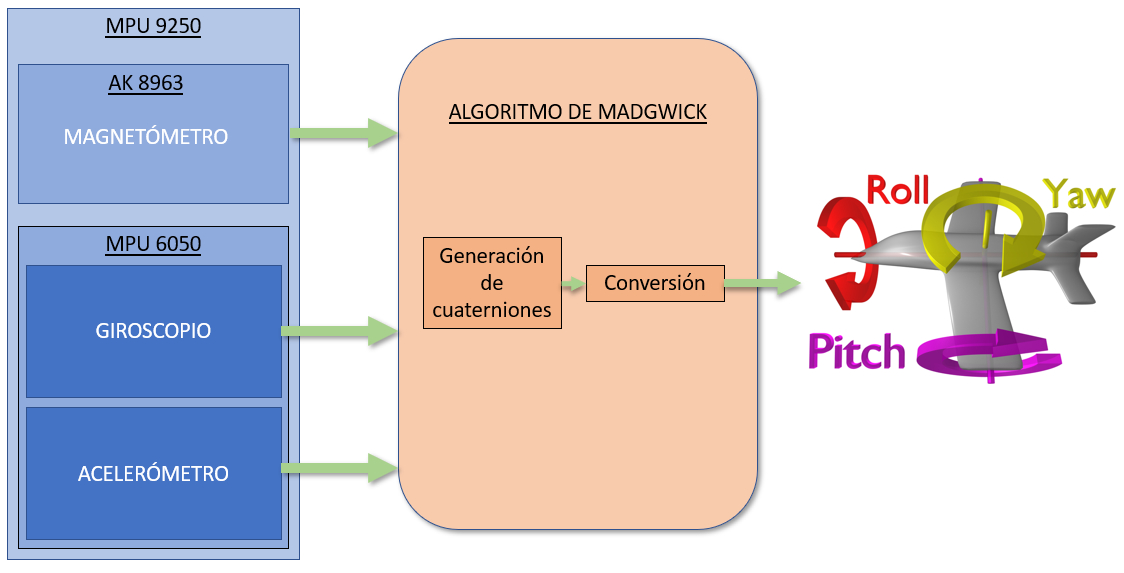
Memoria/Latex/img/yawpitchrollplane.png
