danielss24/TFG_EPS_DSS/Memoria/Latex/img/z0MapaViento.png

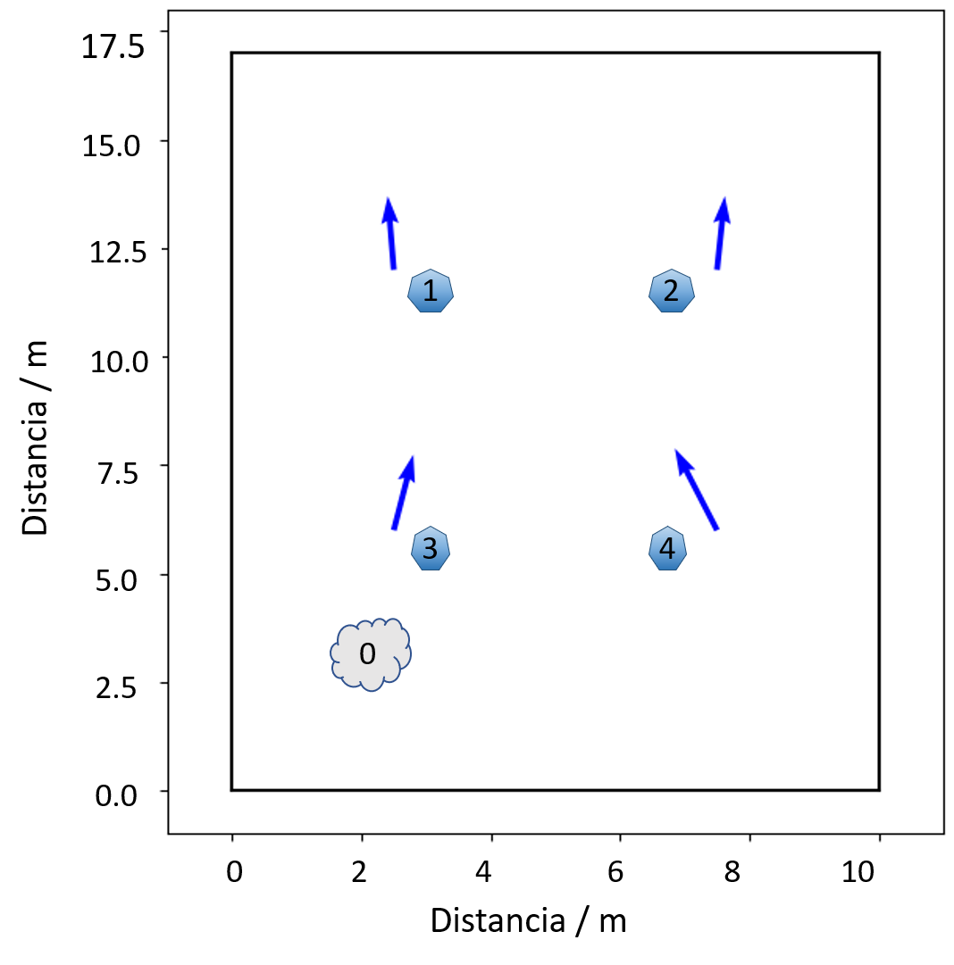
Memoria/Latex/img/z0MapaViento.png
