danielss24/TFG_EPS_DSS/Memoria/Latex/img/z1MapaViento.png

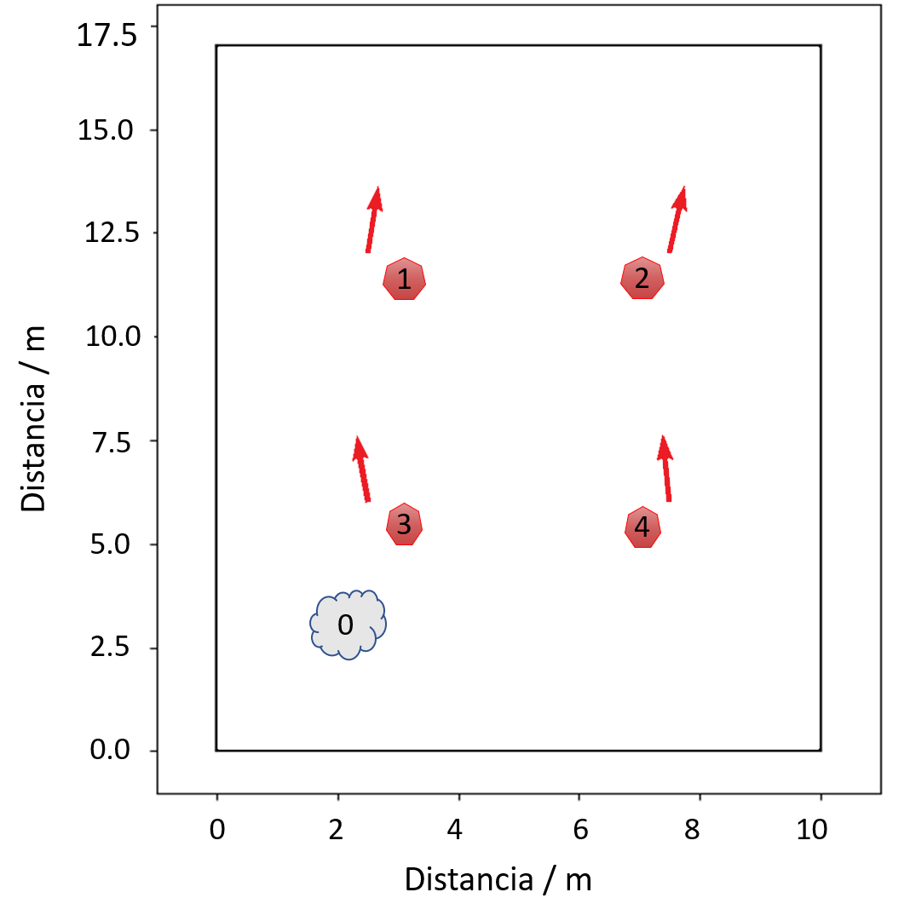
Memoria/Latex/img/z1MapaViento.png
