danielss24/TFG_EPS_DSS/Memoria/referencias anemometros/Cup Anemometer, कप एनीमोमीटर, कप एनेमोमीटर - Electro Mechanical Enterprises, Noida _ ID_ 12493118573_files/anemometer-250x250.jpg

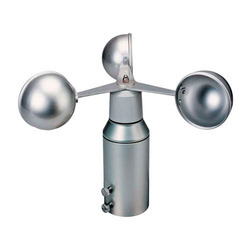
Memoria/referencias anemometros/Cup Anemometer, कप एनीमोमीटर, कप एनेमोमीटर - Electro Mechanical Enterprises, Noida _ ID_ 12493118573_files/anemometer-250x250.jpg
