danielss24/TFG_EPS_DSS/Memoria/referencias anemometros/Extech HD350 Pitot Tube Anemometer Differential Manometer for sale online _ eBay_files/s-l1600(1).jpg

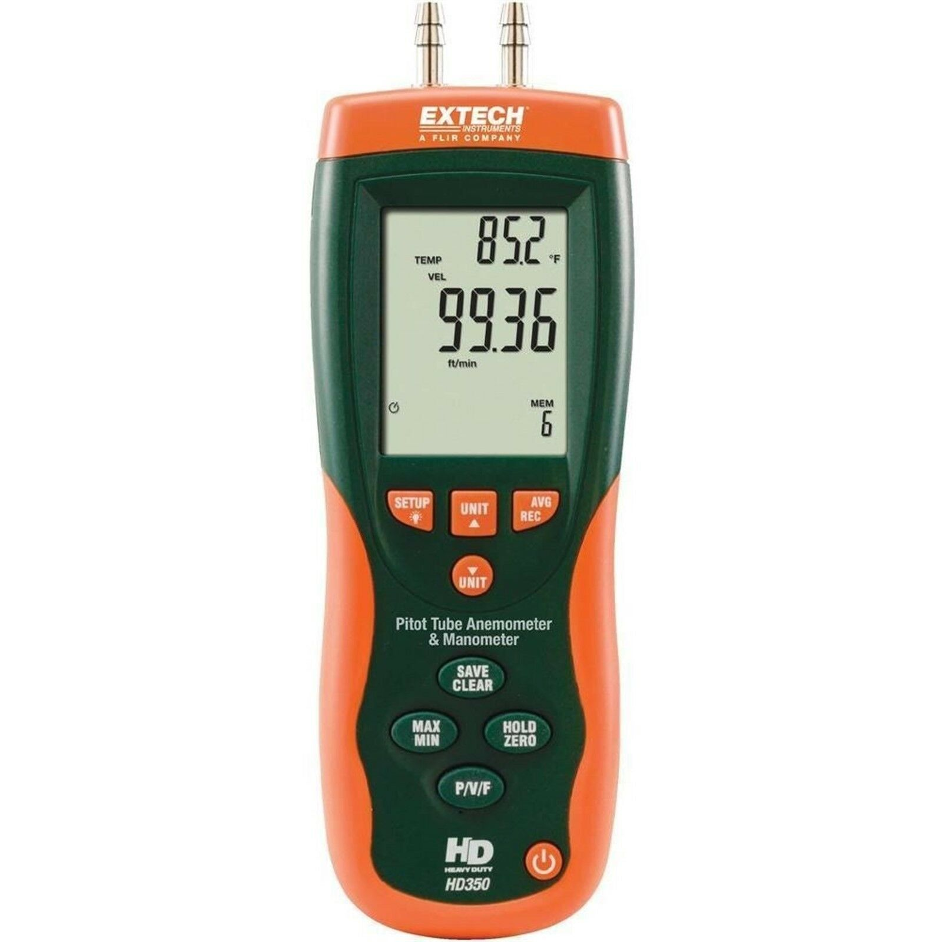
Memoria/referencias anemometros/Extech HD350 Pitot Tube Anemometer Differential Manometer for sale online _ eBay_files/s-l1600(1).jpg
