danielss24/TFG_EPS_DSS/Memoria/referencias anemometros/Five Hole Probe - Flow Direction_files/tunp5h.jpg

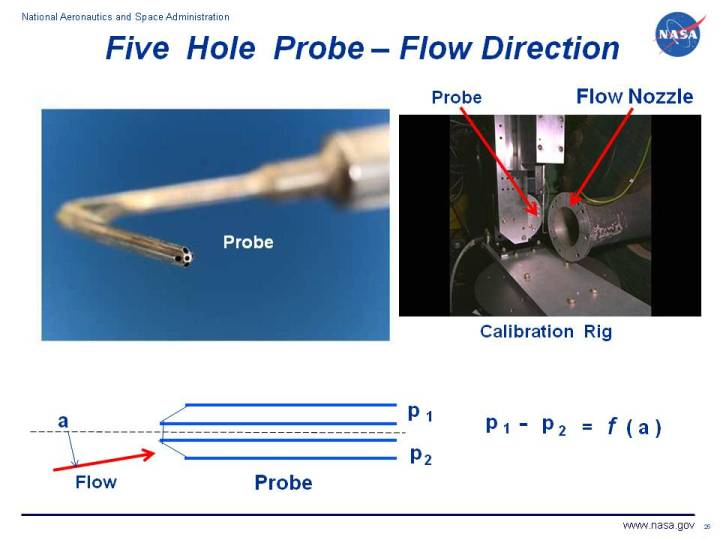
Memoria/referencias anemometros/Five Hole Probe - Flow Direction_files/tunp5h.jpg
