danielss24/TFG_EPS_DSS/Memoria/referencias anemometros/Funcionamiento y tipos de anemómetros_files/pitot.gif

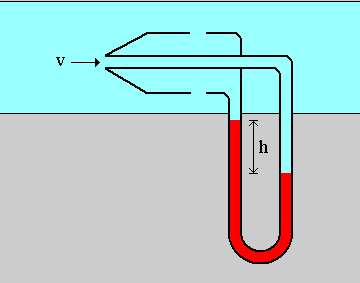
Memoria/referencias anemometros/Funcionamiento y tipos de anemómetros_files/pitot.gif
