danielss24/TFG_EPS_DSS/Memoria/referencias anemometros/Hot Wire Anemometer at Rs 9500 _piece _ George Town _ Chennai _ ID_ 4703246662_files/cup-counter-anemometer-250x250.jpg

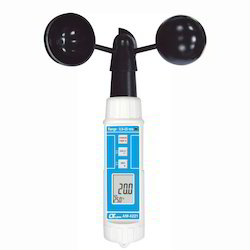
Memoria/referencias anemometros/Hot Wire Anemometer at Rs 9500 _piece _ George Town _ Chennai _ ID_ 4703246662_files/cup-counter-anemometer-250x250.jpg
