danielss24/TFG_EPS_DSS/Memoria/referencias anemometros/Hot Wire Anemometer at Rs 9500 _piece _ George Town _ Chennai _ ID_ 4703246662_files/tam-05spd-hot-wire-anemometer-with-data-logger-250x250.png

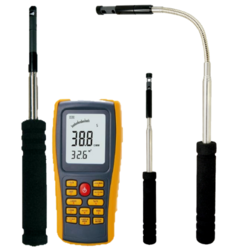
Memoria/referencias anemometros/Hot Wire Anemometer at Rs 9500 _piece _ George Town _ Chennai _ ID_ 4703246662_files/tam-05spd-hot-wire-anemometer-with-data-logger-250x250.png
