danielss24/TFG_EPS_DSS/Memoria/referencias anemometros/Laser-Cantilever-Anemometer — Carl von Ossietzky University of Oldenburg_files/csm_LCA_d8db10098e.png

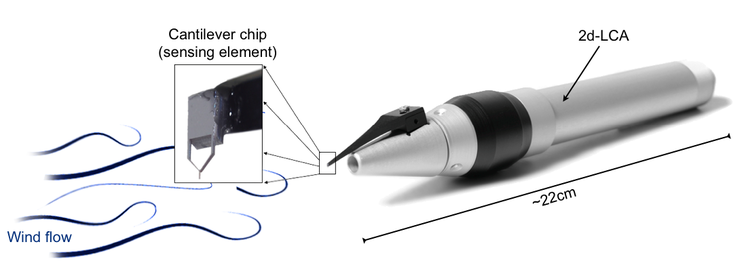
Memoria/referencias anemometros/Laser-Cantilever-Anemometer — Carl von Ossietzky University of Oldenburg_files/csm_LCA_d8db10098e.png
