danielss24/TFG_EPS_DSS/Memoria/referencias anemometros/MASC UAV Flight Analysis _ Unmanned Aerial Vehicle _ Inertial Navigation System_files/1-efecd5b5ef.jpg

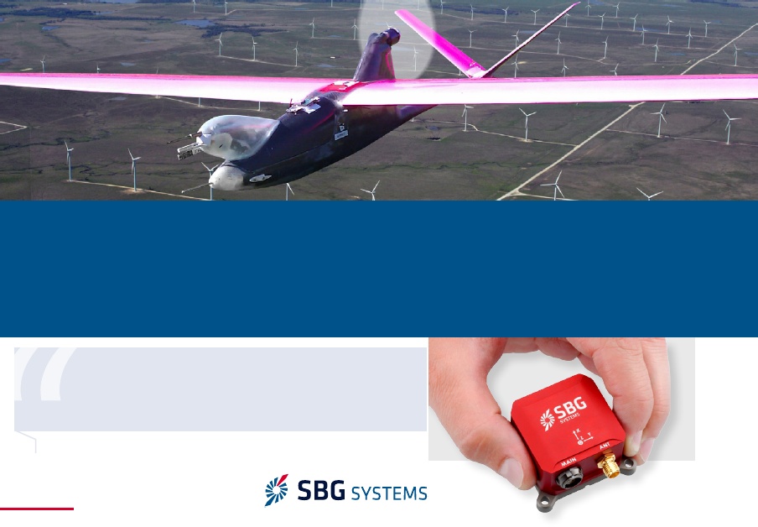
Memoria/referencias anemometros/MASC UAV Flight Analysis _ Unmanned Aerial Vehicle _ Inertial Navigation System_files/1-efecd5b5ef.jpg
