danielss24/TFG_EPS_DSS/Memoria/referencias anemometros/MASC UAV Flight Analysis _ Unmanned Aerial Vehicle _ Inertial Navigation System_files/table_reading.png

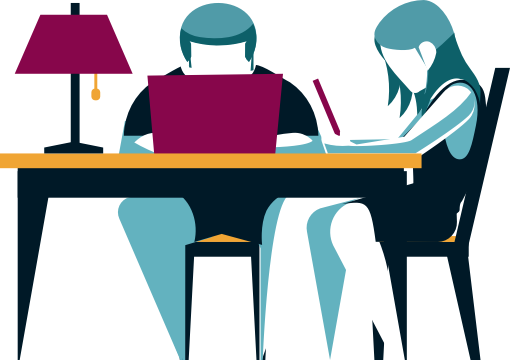
Memoria/referencias anemometros/MASC UAV Flight Analysis _ Unmanned Aerial Vehicle _ Inertial Navigation System_files/table_reading.png
