danielss24/TFG_EPS_DSS/Memoria/referencias anemometros/Sphereanemometer — Carl von Ossietzky University of Oldenburg_files/RTEmagicC_9f80848d96.jpg.jpg

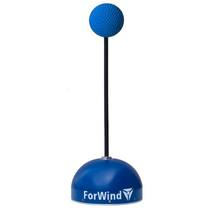
Memoria/referencias anemometros/Sphereanemometer — Carl von Ossietzky University of Oldenburg_files/RTEmagicC_9f80848d96.jpg.jpg
