danielss24/TFG_EPS_DSS/Memoria/referencias anemometros/Ultrasonic Anemometer 2D _ 4.3820.xx.xx _ Biral_files/4.3820-315x289.png

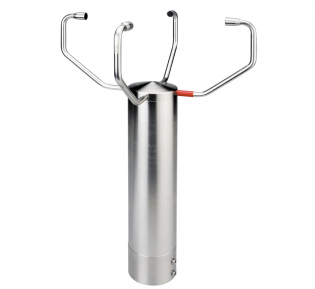
Memoria/referencias anemometros/Ultrasonic Anemometer 2D _ 4.3820.xx.xx _ Biral_files/4.3820-315x289.png
