danielss24/TFG_EPS_DSS/Memoria/referencias anemometros/Ultrasonic Anemometer 2D _ 4.3820.xx.xx _ Biral_files/ultrasonic-compact4.3871.0x.xxx_-225x225.png

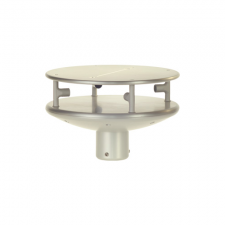
Memoria/referencias anemometros/Ultrasonic Anemometer 2D _ 4.3820.xx.xx _ Biral_files/ultrasonic-compact4.3871.0x.xxx_-225x225.png
