danielss24/TFG_EPS_DSS/Memoria/referencias anemometros/XLC V2 lifting helicopter_files/31599_0.JPG

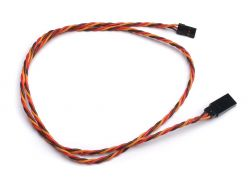
Memoria/referencias anemometros/XLC V2 lifting helicopter_files/31599_0.JPG
