danielss24/TFG_EPS_DSS/Memoria/referencias anemometros/XLC V2 lifting helicopter_files/100031_2.jpg

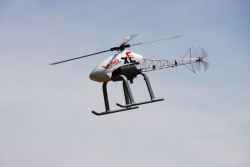
Memoria/referencias anemometros/XLC V2 lifting helicopter_files/100031_2.jpg
