danielss24/TFG_EPS_DSS/Memoria/referencias anemometros/XLC V2 lifting helicopter_files/101741_0.JPG

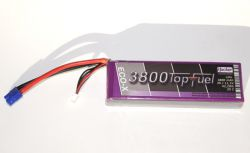
Memoria/referencias anemometros/XLC V2 lifting helicopter_files/101741_0.JPG
