danielss24/TFG_EPS_DSS/Programa/2019/06/03/Plot/144618_Plot4.png

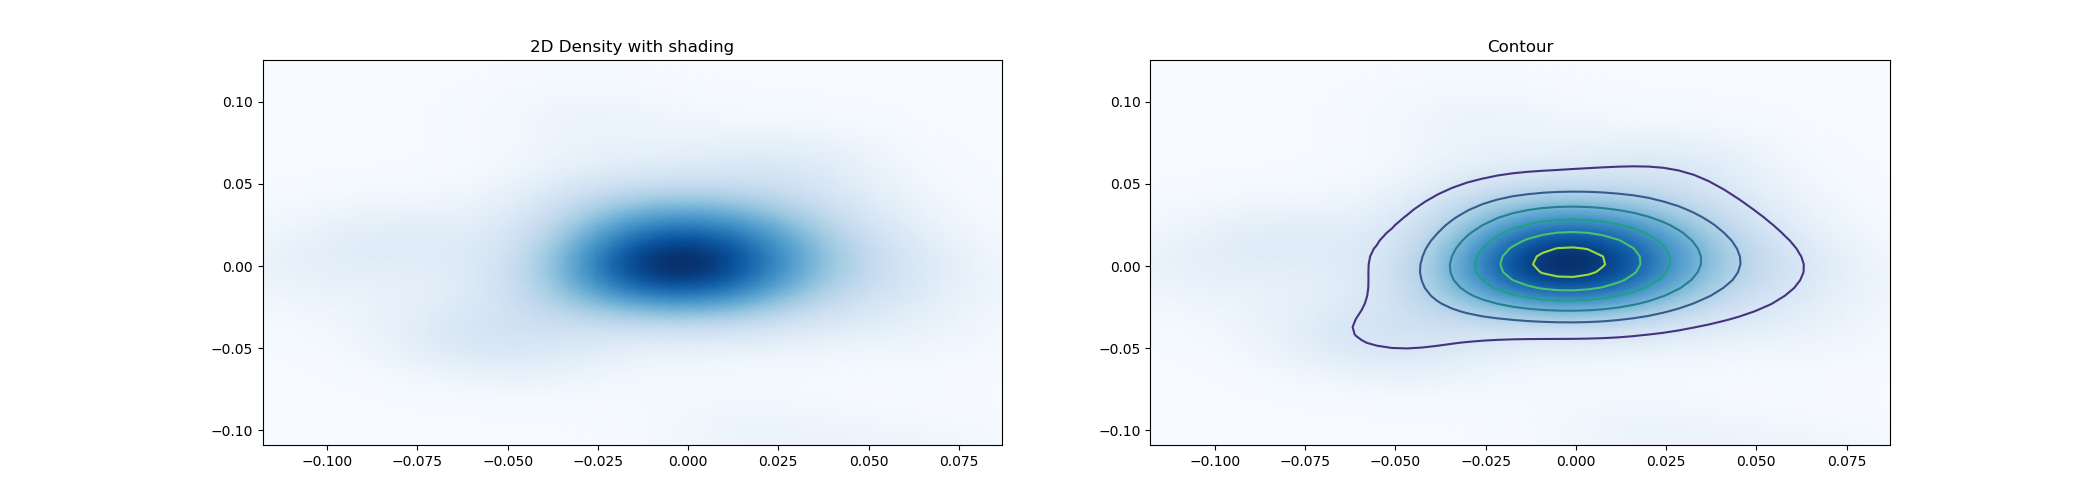
Programa/2019/06/03/Plot/144618_Plot4.png
