danielss24/TFG_EPS_DSS/Programa/2019/06/03/Plot/144752_Plot3.png

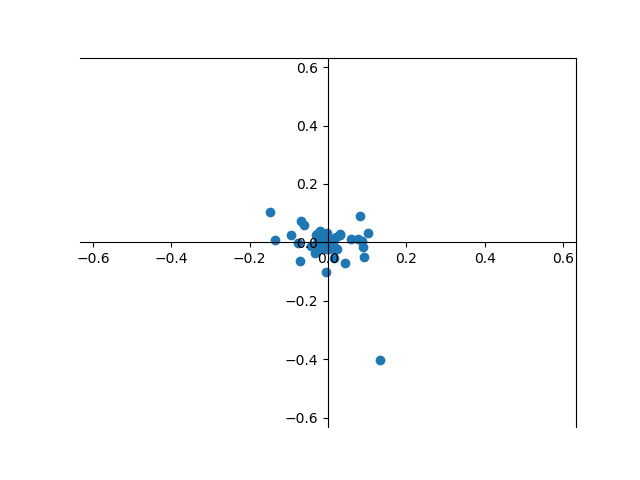
Programa/2019/06/03/Plot/144752_Plot3.png
