danielss24/TFG_EPS_DSS/Programa/2019/06/03/Plot/150608_Plot6.png

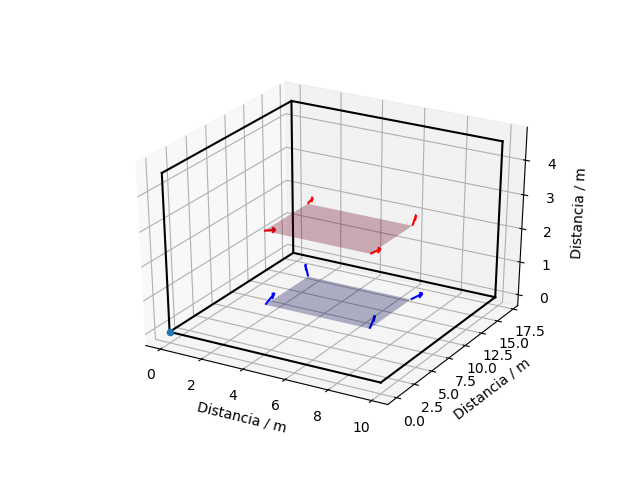
Programa/2019/06/03/Plot/150608_Plot6.png
