danielss24/TFG_EPS_DSS/Programa/2019/06/03/Plot/Pack/z0/144523_Plot2.png

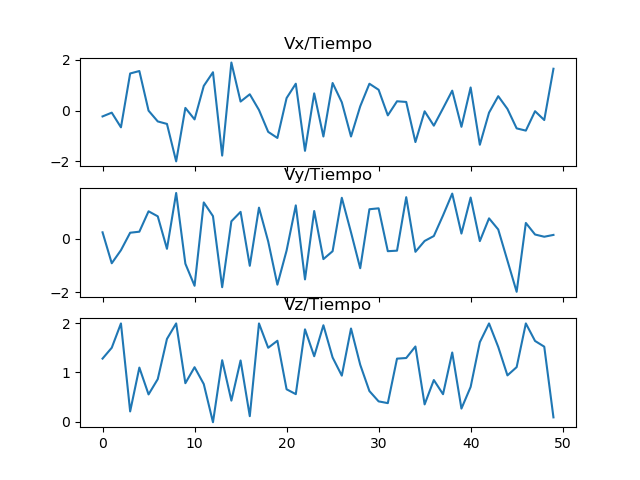
Programa/2019/06/03/Plot/Pack/z0/144523_Plot2.png
