danielss24/TFG_EPS_DSS/Programa/2019/06/05/Plot/151239_Plot3.png

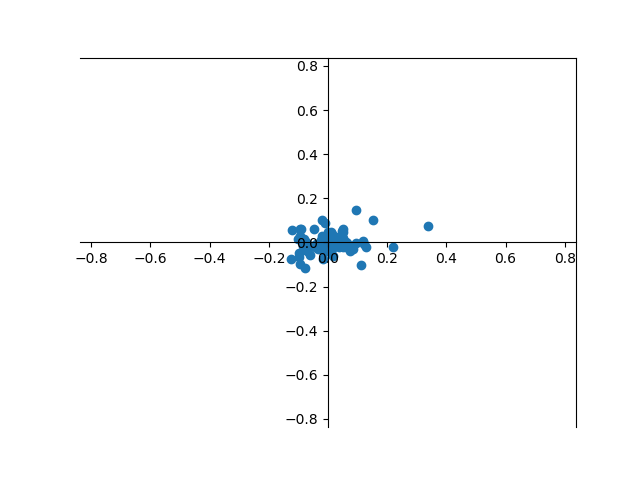
Programa/2019/06/05/Plot/151239_Plot3.png
