danielss24/TFG_EPS_DSS/Programa/2019/06/05/Plot/151652_Plot4.png

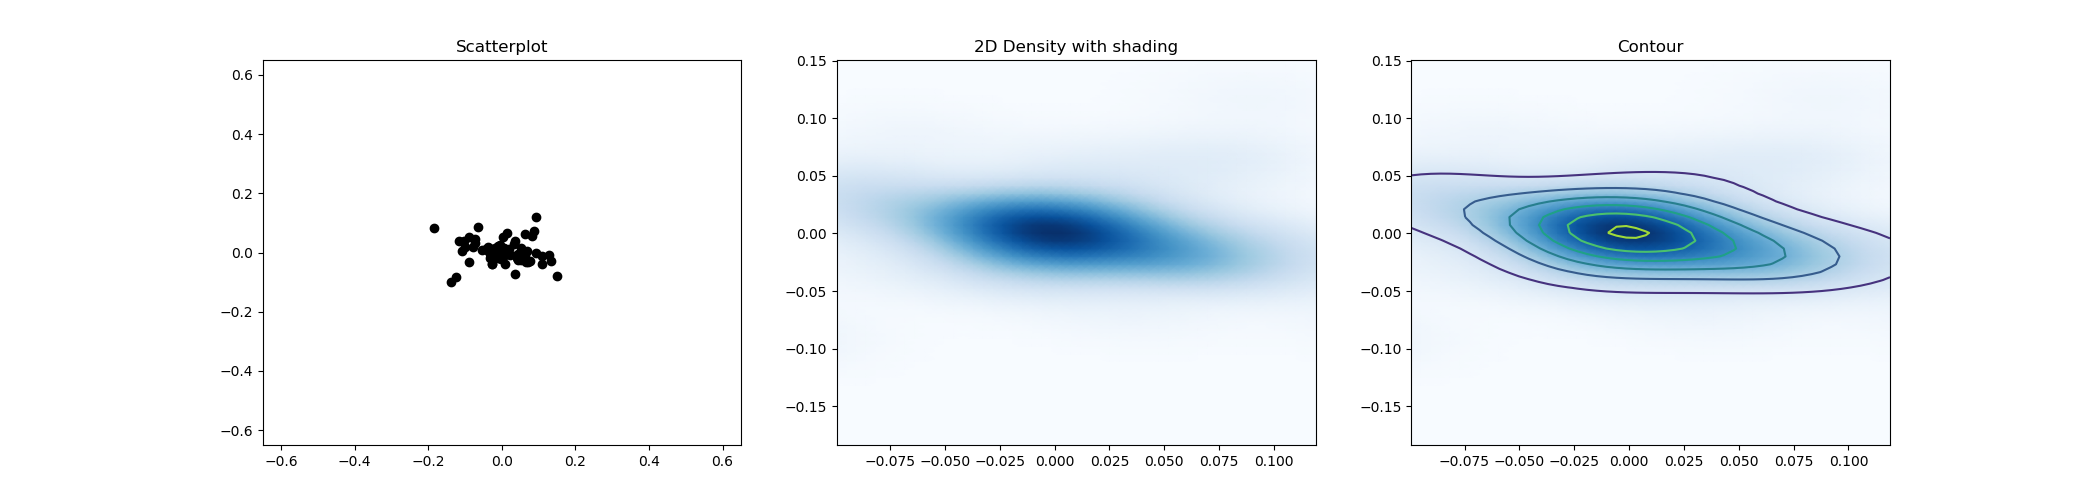
Programa/2019/06/05/Plot/151652_Plot4.png
