danielss24/TFG_EPS_DSS/Programa/2019/06/05/Plot/151828_Plot2.png

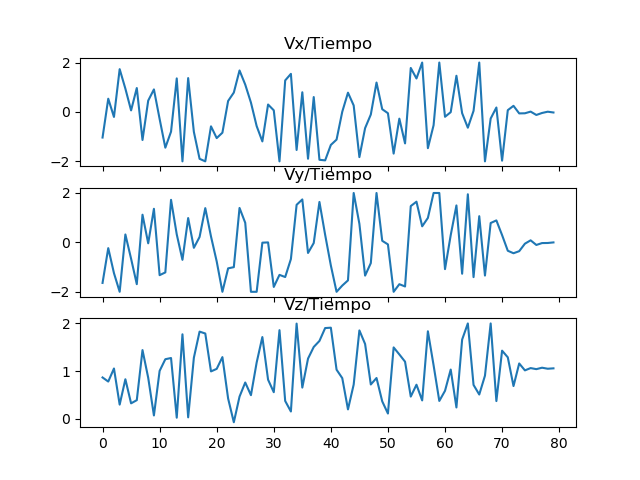
Programa/2019/06/05/Plot/151828_Plot2.png
