danielss24/TFG_EPS_DSS/Programa/2019/06/09/Plot/115909_Plot4.png

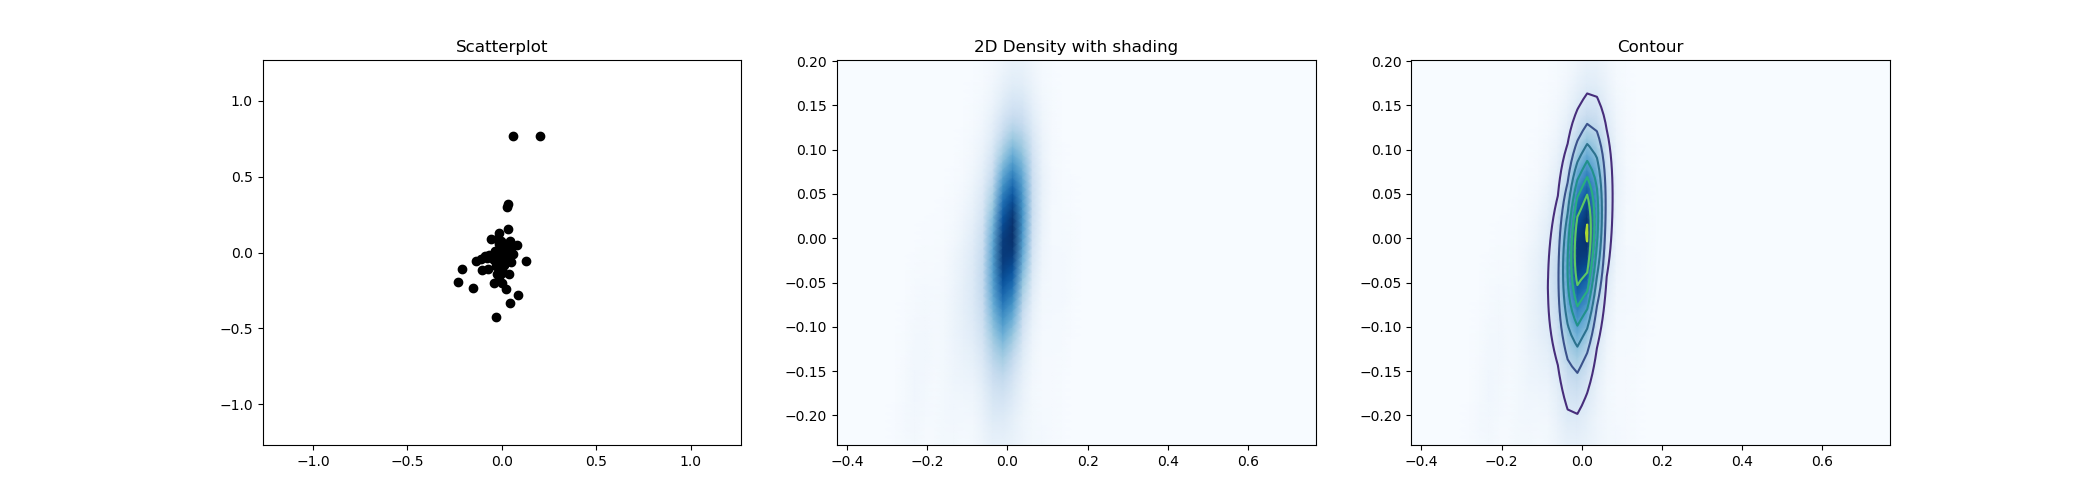
Programa/2019/06/09/Plot/115909_Plot4.png
