danielss24/TFG_EPS_DSS/Modelos3D/Inventor3DModel/STL/PataDronSD_mk2.stl

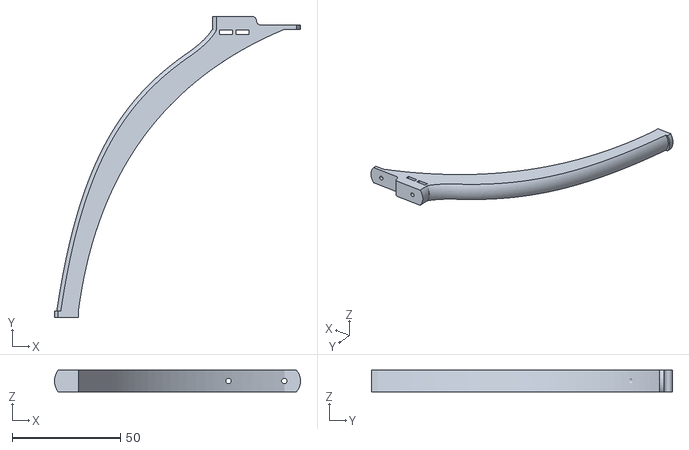
[picture p229: CAD file, 2019-04-23]
Modelos3D/Inventor3DModel/STL/PataDronSD_mk2.stl
113.5 x 139.0 x 10.0
