danielss24/TFG_EPS_DSS/Modelos3D/Inventor3DModel/STL/Folks/HablarEsFundamental.stl

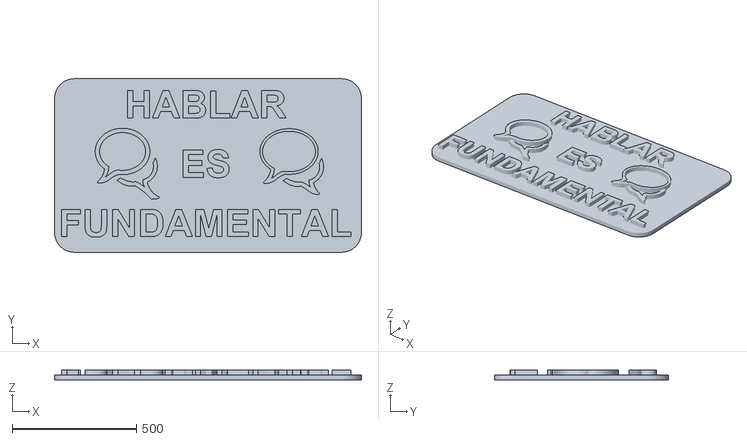
[picture p230: CAD file, 2019-04-23]
Modelos3D/Inventor3DModel/STL/Folks/HablarEsFundamental.stl
1233.0 x 697.4 x 40.0
