danielss24/TFG_EPS_DSS/Modelos3D/Inventor3DModel/STL/xyzCalibration_cube.stl

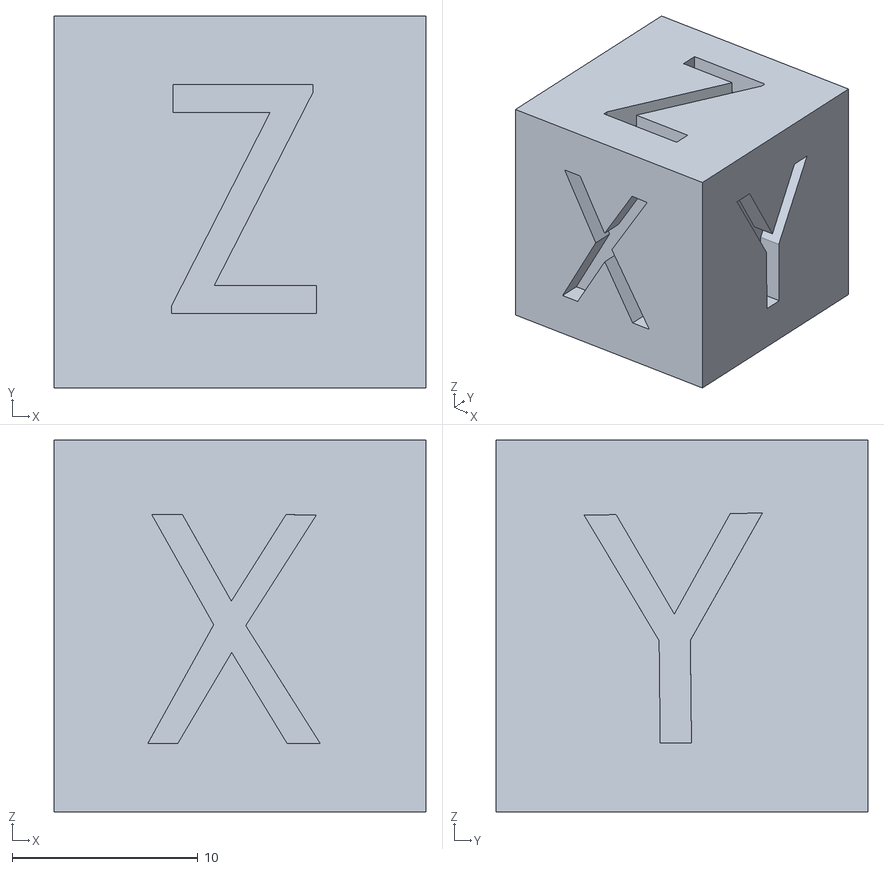
[picture p231: CAD file, 2019-04-23]
Modelos3D/Inventor3DModel/STL/xyzCalibration_cube.stl
20.0 x 20.0 x 20.0
