danielss24/TFG_EPS_DSS/Modelos3D/Inventor3DModel/STL/Folks/mausah.stl

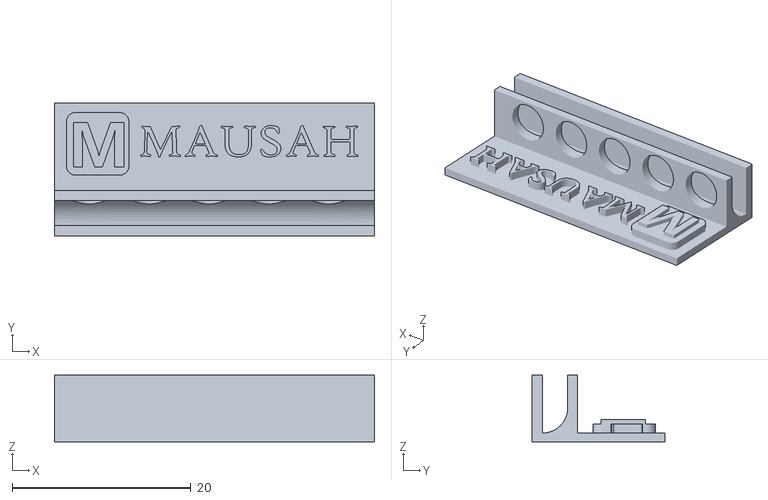
[picture p232: CAD file, 2019-04-23]
Modelos3D/Inventor3DModel/STL/Folks/mausah.stl
35.9 x 14.9 x 7.50
