danielss24/TFG_EPS_DSS/Modelos3D/Inventor3DModel/STL/SeparadorRoscado.stl

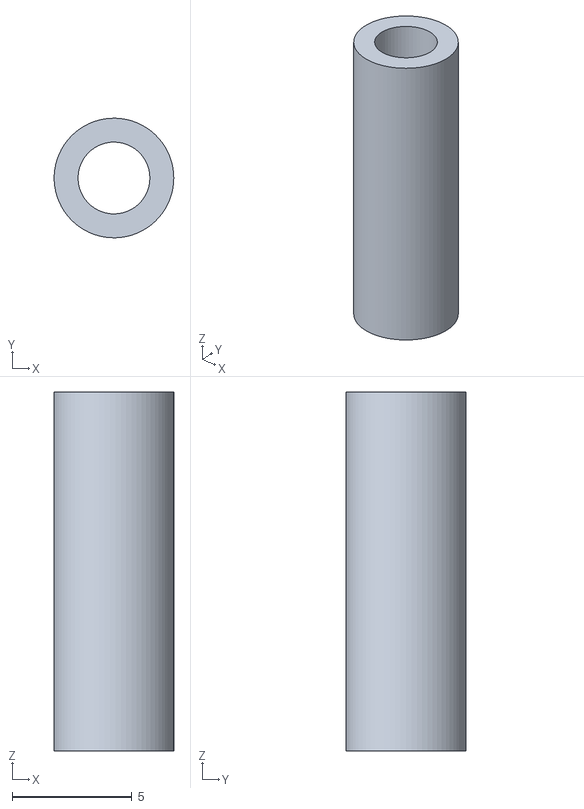
[picture p233: CAD file, 2019-04-23]
Modelos3D/Inventor3DModel/STL/SeparadorRoscado.stl
5.00 x 5.00 x 15.0
