danielss24/TFG_EPS_DSS/Modelos3D/Inventor3DModel/STL/Folks/LearningByBurning2.stl

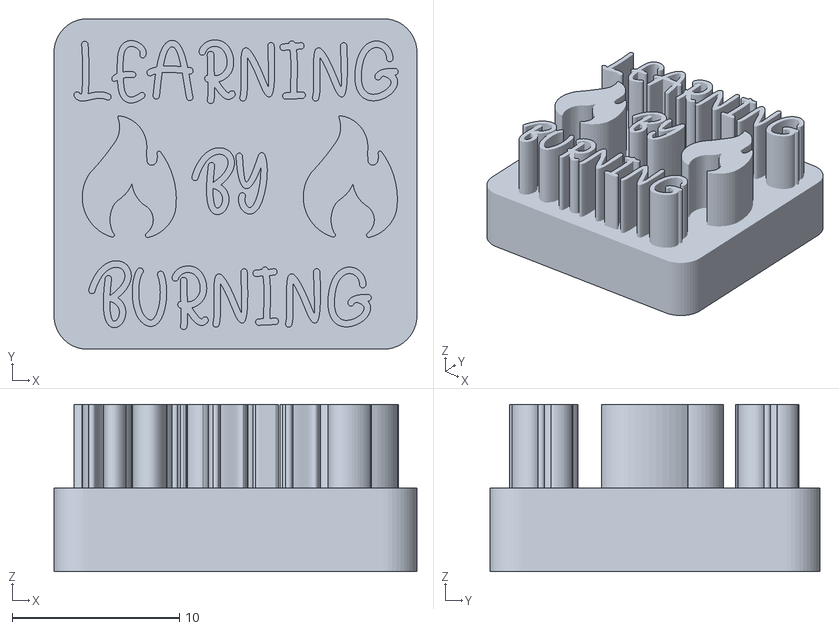
[picture p234: CAD file, 2019-04-23]
Modelos3D/Inventor3DModel/STL/Folks/LearningByBurning2.stl
21.7 x 19.8 x 10.0
