danielss24/TFG_EPS_DSS/Memoria/Latex/img/TapaIntermediaDronMeasure.PNG

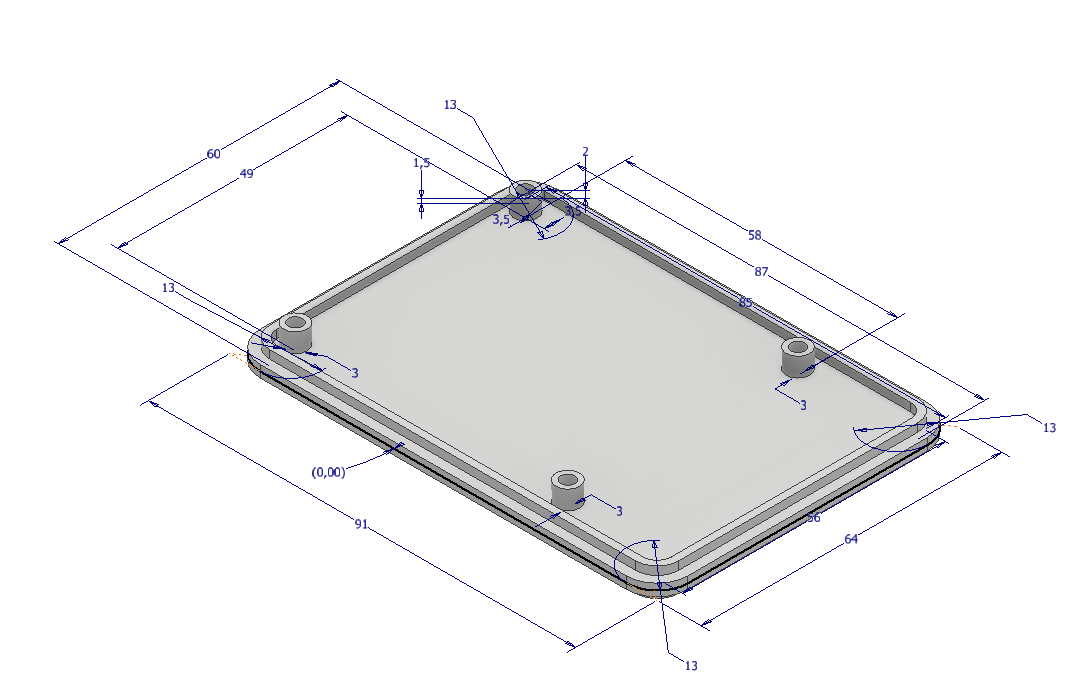
Memoria/Latex/img/TapaIntermediaDronMeasure.PNG
