danielss24/TFG_EPS_DSS/Programa/Pckg/S2/MPU9250/Quaternion.py

__author__ = 'Geir Istad'
"""
MPU6050 Python I2C Class
Copyright (c) 2015 Geir Istad

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

Code based on
I2Cdev library collection - 3D math helper
by Jeff Rowberg <jeff@rowberg.net>
============================================
I2Cdev device library code is placed under the MIT license
Copyright (c) 2012 Jeff Rowberg
Permission is hereby granted, free of charge, to any person obtaining a copy
of this software and associated documentation files (the "Software"), to deal
in the Software without restriction, including without limitation the rights
to use, copy, modify, merge, publish, distribute, sublicense, and/or sell
copies of the Software, and to permit persons to whom the Software is
furnished to do so, subject to the following conditions:
The above copyright notice and this permission notice shall be included in
all copies or substantial portions of the Software.
THE SOFTWARE IS PROVIDED "AS IS", WITHOUT WARRANTY OF ANY KIND, EXPRESS OR
IMPLIED, INCLUDING BUT NOT LIMITED TO THE WARRANTIES OF MERCHANTABILITY,
FITNESS FOR A PARTICULAR PURPOSE AND NONINFRINGEMENT. IN NO EVENT SHALL THE
AUTHORS OR COPYRIGHT HOLDERS BE LIABLE FOR ANY CLAIM, DAMAGES OR OTHER
LIABILITY, WHETHER IN AN ACTION OF CONTRACT, TORT OR OTHERWISE, ARISING FROM,
OUT OF OR IN CONNECTION WITH THE SOFTWARE OR THE USE OR OTHER DEALINGS IN
THE SOFTWARE.
===============================================
"""
from math import sqrt


class Quaternion:
    w = 0.0
    x = 0.0
    y = 0.0
    z = 0.0

    def __init__(self, a_w=1.0, a_x=0.0, a_y=0.0, a_z=0.0):
        self.w = a_w
        self.x = a_x
        self.y = a_y
        self.z = a_z

    def get_product(self, a_quat):
        result = Quaternion(
            self.w * a_quat.w - self.x * a_quat.x -
            self.y * a_quat.y - self.z * a_quat.z,

            self.w * a_quat.x + self.x * a_quat.w +
            self.y * a_quat.z - self.z * a_quat.y,

            self.w * a_quat.y - self.x * a_quat.z +
            self.y * a_quat.w + self.z * a_quat.x,

            self.w * a_quat.z + self.x * a_quat.y -
            self.y * a_quat.x + self.z * a_quat.w)
        return result

    def get_conjugate(self):
        result = Quaternion(self.w, -self.x, -self.y, -self.z)
        return result

    def get_magnitude(self):
        return sqrt(self.w * self.w + self.x * self.x + self.y * self.y +
                    self.z * self.z)

    def normalize(self):
        m = self.get_magnitude()
        self.w = self.w / m
        self.x = self.x / m
        self.y = self.y / m
        self.z = self.z / m

    def get_normalized(self):
        result = Quaternion(self.w, self.x, self.y, self.z)
        result.normalize()
        return result


class XYZVector:
    x = 0.0
    y = 0.0
    z = 0.0

    def __init__(self, a_x=0.0, a_y=0.0, a_z=0.0):
        self.x = a_x
        self.y = a_y
        self.z = a_z

    def get_magnitude(self):
        return sqrt(self.x*self.x + self.y*self.y + self.z*self.z)

    def normalize(self):
        m = self.get_magnitude()
        self.x = self.x / m
        self.y = self.y / m
        self.z = self.z / m

    def get_normalized(self):
        result = XYZVector(self.x, self.y, self.z)
        result.normalize()
        return result

    def rotate(self, a_quat):
        p = Quaternion(0.0, self.x, self.y, self.z)
        p = a_quat.get_product(p)
        p = p.get_product(a_quat.get_conjugate())
        # By magic quaternion p is now [0, x', y', z']
        self.x = p.x
        self.y = p.y
        self.z = p.z

    def get_rotated(self, a_quat):
        r = XYZVector(self.x, self.y, self.z)
        r.rotate(a_quat)
        return r

    def toString(self):
        return str(self.x,self.y,self.z)
